azonenberg/dumptruck/dut-breakouts/parallel-nor-csp56/parallel-nor-csp56.kicad_pcb

## KiCad design dut-breakouts/parallel-nor-csp56/parallel-nor-csp56.kicad_pcb (2024-11-30)

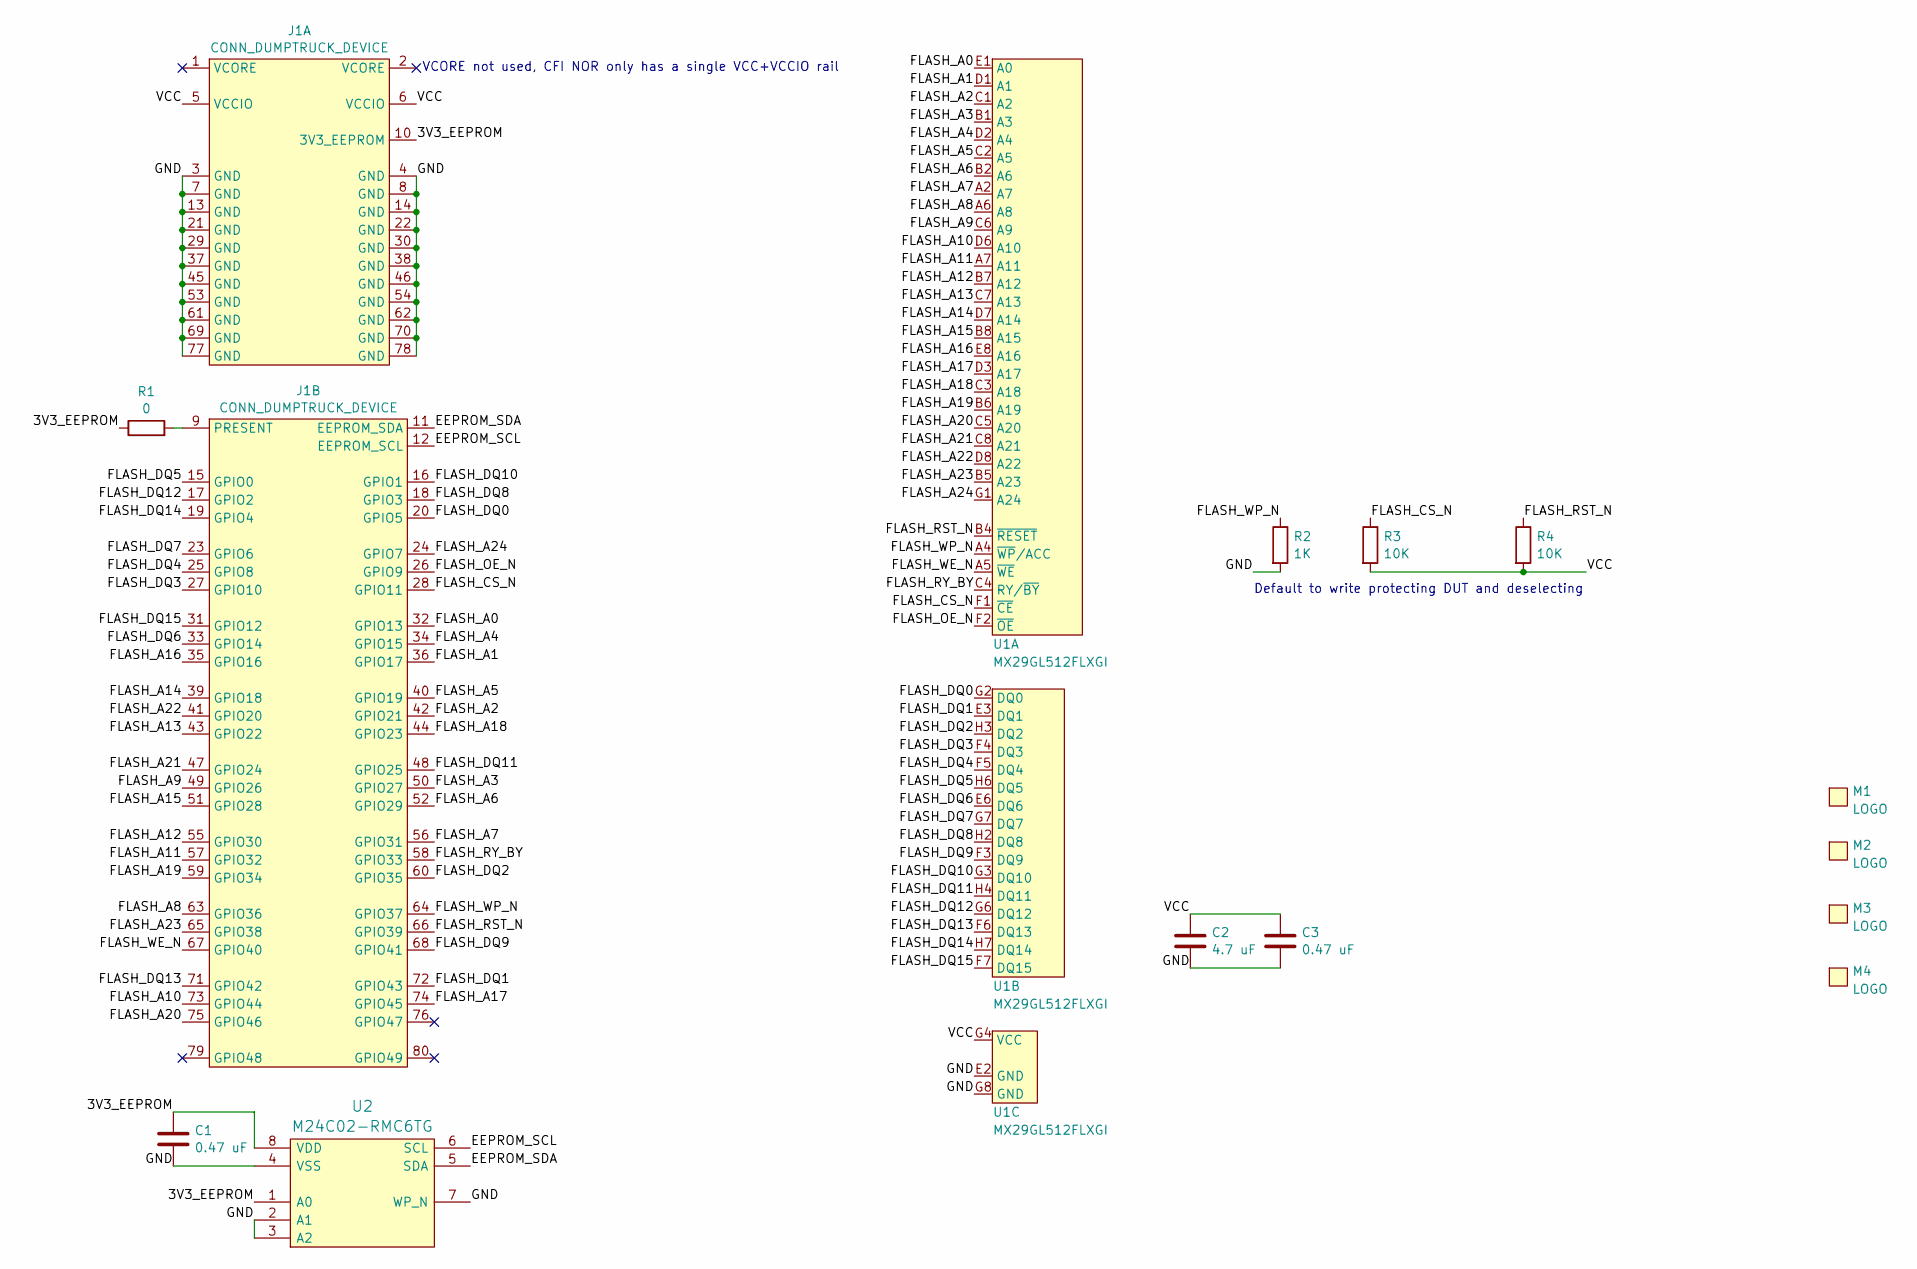
[picture p22: schematic parallel-nor-csp56.kicad_sch]

Parts:
C1, C3: 0.47 uF; EIA_0402_CAP_NOSILK
C2: 4.7 uF; EIA_0603_CAP_NOSILK
J1: CONN_DUMPTRUCK_DEVICE; CONN_SAMTEC_BSE-040-01-L-D-A-TR
M1: LOGO; LONGTHING-1200DPI
M2: LOGO; Logo_silk_ROHS_5x2.8mm
M3: LOGO; Logo_silk_OSHW_6x6mm
M4: LOGO; Logo_silk_WEEE_3.4x5mm
R1: 0; EIA_0402_RES_NOSILK
R2: 1K; EIA_0402_RES_NOSILK
R3, R4: 10K; EIA_0402_RES_NOSILK
U1: MX29GL512FLXGI; BGA_56_6x9_DEPOP_0.8MM_CFI_CSP
U2: M24C02-RMC6TG; DFN_8_0.5MM_2x3MM_TALL

Connections:
/3V3_EEPROM: C1.1, J1.10 (3V3_EEPROM), R1.1, U2.1 (A0), U2.8 (VDD)
/EEPROM_SCL: J1.12 (EEPROM_SCL), U2.6 (SCL)
/EEPROM_SDA: J1.11 (EEPROM_SDA), U2.5 (SDA)
/FLASH_A0: J1.32 (GPIO13), U1.E1 (A0)
/FLASH_A1: J1.36 (GPIO17), U1.D1 (A1)
/FLASH_A2: J1.42 (GPIO21), U1.C1 (A2)
/FLASH_A3: J1.50 (GPIO27), U1.B1 (A3)
/FLASH_A4: J1.34 (GPIO15), U1.D2 (A4)
/FLASH_A5: J1.40 (GPIO19), U1.C2 (A5)
/FLASH_A6: J1.52 (GPIO29), U1.B2 (A6)
/FLASH_A7: J1.56 (GPIO31), U1.A2 (A7)
/FLASH_A8: J1.63 (GPIO36), U1.A6 (A8)
/FLASH_A9: J1.49 (GPIO26), U1.C6 (A9)
/FLASH_A10: J1.73 (GPIO44), U1.D6 (A10)
/FLASH_A11: J1.57 (GPIO32), U1.A7 (A11)
/FLASH_A12: J1.55 (GPIO30), U1.B7 (A12)
/FLASH_A13: J1.43 (GPIO22), U1.C7 (A13)
/FLASH_A14: J1.39 (GPIO18), U1.D7 (A14)
/FLASH_A15: J1.51 (GPIO28), U1.B8 (A15)
/FLASH_A16: J1.35 (GPIO16), U1.E8 (A16)
/FLASH_A17: J1.74 (GPIO45), U1.D3 (A17)
/FLASH_A18: J1.44 (GPIO23), U1.C3 (A18)
/FLASH_A19: J1.59 (GPIO34), U1.B6 (A19)
/FLASH_A20: J1.75 (GPIO46), U1.C5 (A20)
/FLASH_A21: J1.47 (GPIO24), U1.C8 (A21)
/FLASH_A22: J1.41 (GPIO20), U1.D8 (A22)
/FLASH_A23: J1.65 (GPIO38), U1.B5 (A23)
/FLASH_A24: J1.24 (GPIO7), U1.G1 (A24)
/FLASH_CS_N: J1.28 (GPIO11), R3.1, U1.F1 (~CE)
/FLASH_DQ0: J1.20 (GPIO5), U1.G2 (DQ0)
/FLASH_DQ1: J1.72 (GPIO43), U1.E3 (DQ1)
/FLASH_DQ2: J1.60 (GPIO35), U1.H3 (DQ2)
/FLASH_DQ3: J1.27 (GPIO10), U1.F4 (DQ3)
/FLASH_DQ4: J1.25 (GPIO8), U1.F5 (DQ4)
/FLASH_DQ5: J1.15 (GPIO0), U1.H6 (DQ5)
/FLASH_DQ6: J1.33 (GPIO14), U1.E6 (DQ6)
/FLASH_DQ7: J1.23 (GPIO6), U1.G7 (DQ7)
/FLASH_DQ8: J1.18 (GPIO3), U1.H2 (DQ8)
/FLASH_DQ9: J1.68 (GPIO41), U1.F3 (DQ9)
/FLASH_DQ10: J1.16 (GPIO1), U1.G3 (DQ10)
/FLASH_DQ11: J1.48 (GPIO25), U1.H4 (DQ11)
/FLASH_DQ12: J1.17 (GPIO2), U1.G6 (DQ12)
/FLASH_DQ13: J1.71 (GPIO42), U1.F6 (DQ13)
/FLASH_DQ14: J1.19 (GPIO4), U1.H7 (DQ14)
/FLASH_DQ15: J1.31 (GPIO12), U1.F7 (DQ15)
/FLASH_OE_N: J1.26 (GPIO9), U1.F2 (~OE)
/FLASH_RST_N: J1.66 (GPIO39), R4.1, U1.B4 (~RESET)
/FLASH_RY_BY: J1.58 (GPIO33), U1.C4 (RY/~BY)
/FLASH_WE_N: J1.67 (GPIO40), U1.A5 (~WE)
/FLASH_WP_N: J1.64 (GPIO37), R2.1, U1.A4 (~WP/ACC)
/GND: C1.2, C2.2, C3.2, J1.3 (GND), J1.4 (GND), J1.7 (GND), J1.8 (GND), J1.13 (GND), J1.14 (GND), J1.21 (GND), J1.22 (GND), J1.29 (GND), J1.30 (GND), J1.37 (GND), J1.38 (GND), J1.45 (GND), J1.46 (GND), J1.53 (GND), J1.54 (GND), J1.61 (GND), J1.62 (GND), J1.69 (GND), J1.70 (GND), J1.77 (GND), J1.78 (GND), R2.2, U1.E2 (GND), U1.G8 (GND), U2.2 (A1), U2.3 (A2), U2.4 (VSS), U2.7 (WP_N)
/VCC: C2.1, C3.1, J1.5 (VCCIO), J1.6 (VCCIO), R3.2, R4.2, U1.G4 (VCC)
unnamed: J1.9 (PRESENT), R1.2

Notes on the sheet:
VCORE not used, CFI NOR only has a single VCC+VCCIO rail
Default to write protecting DUT and deselecting

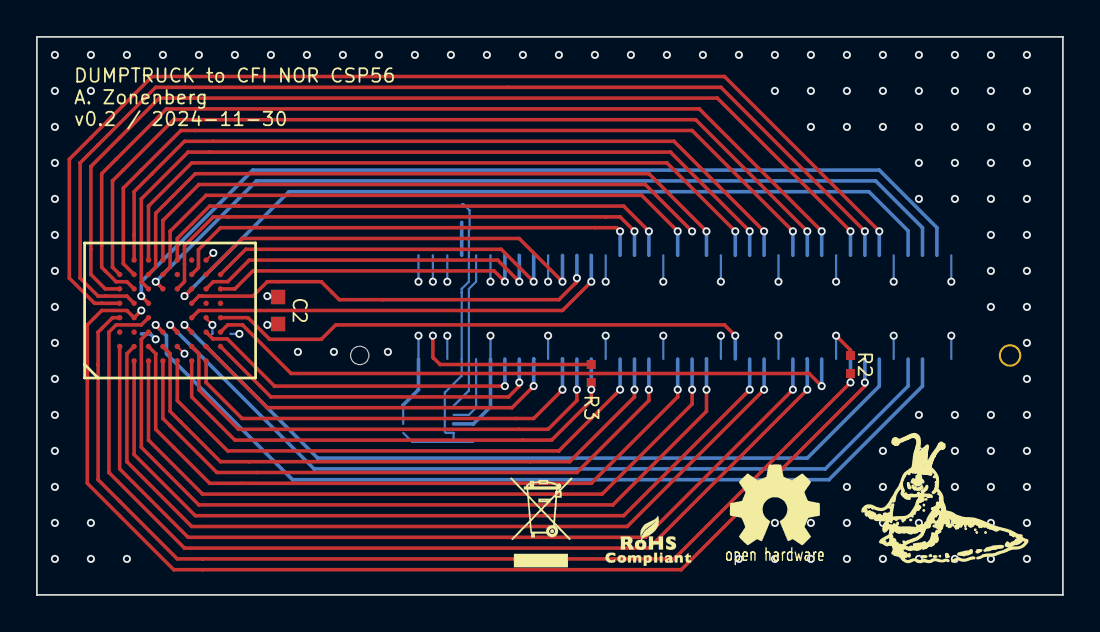
[picture p23: board parallel-nor-csp56.kicad_pcb from above]

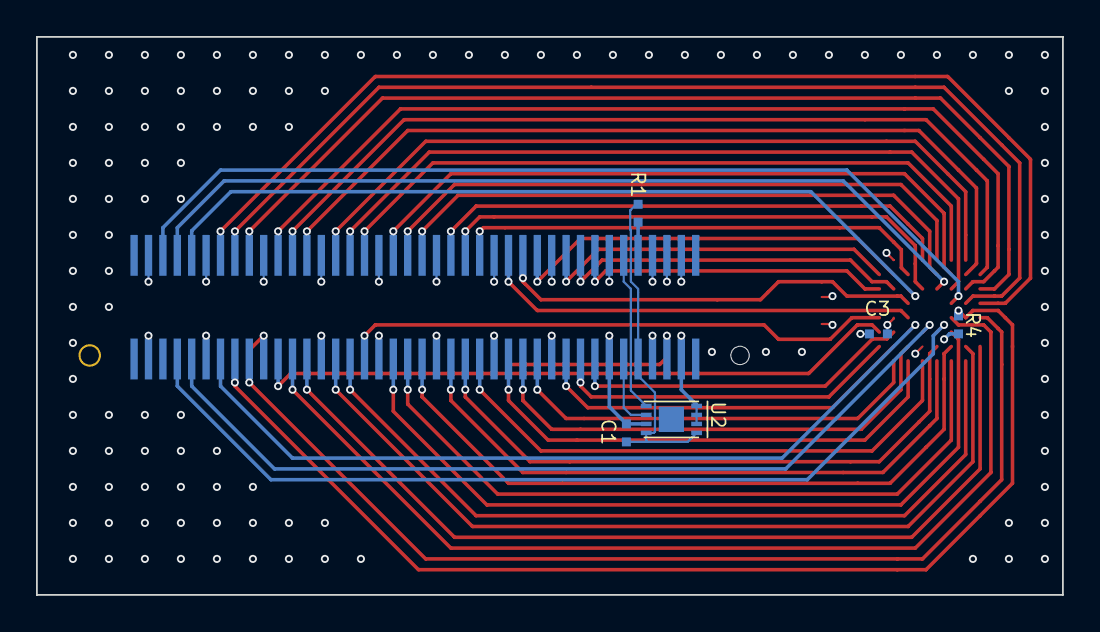
[picture p24: board parallel-nor-csp56.kicad_pcb from below]

Board: 4 copper layers, 57.0 x 31.0 mm, 14 parts (6 on the bottom side), 53 nets.
