azonenberg/dumptruck/jtag-interposer/jtag-interposer.kicad_pcb

## KiCad design jtag-interposer/jtag-interposer.kicad_pcb (2024-11-25)

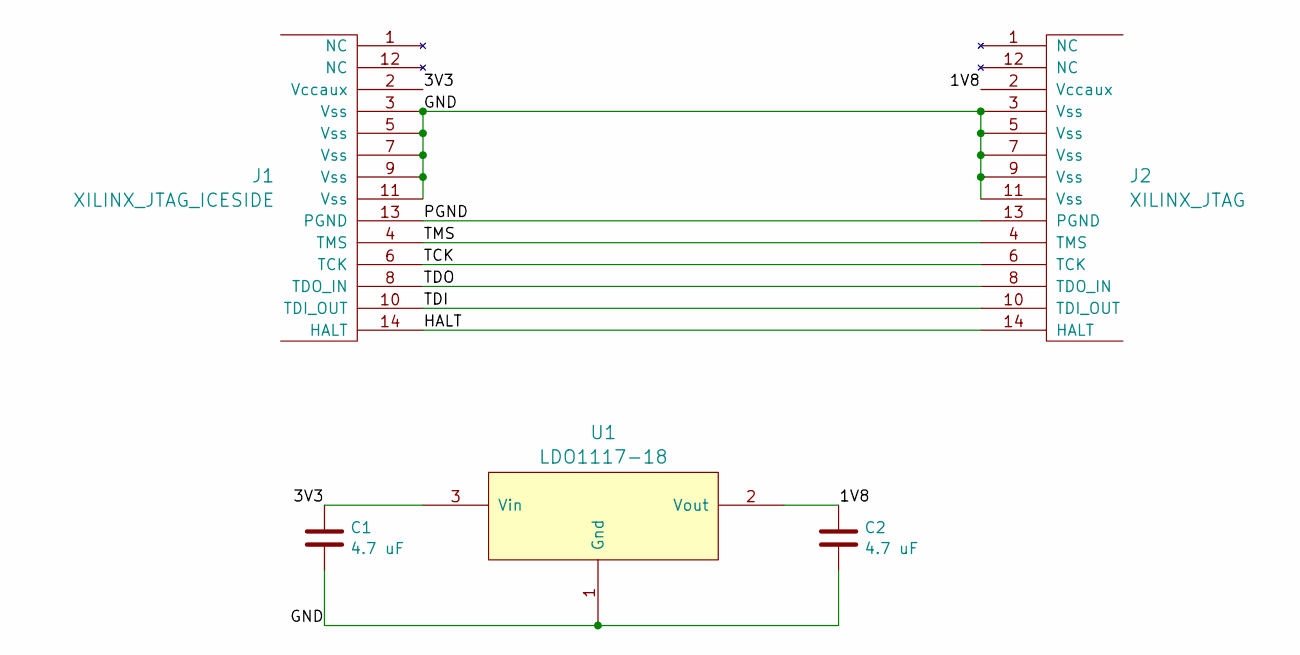
[picture p25: schematic jtag-interposer.kicad_sch]

Parts:
C1, C2: 4.7 uF; EIA_0603_CAP_NOSILK
J1: XILINX_JTAG_ICESIDE; XILINX_JTAG_PTH_MOLEX_0878311420
J2: XILINX_JTAG; XILINX_JTAG_PTH_MOLEX_0878311420
U1: LDO1117-18; SOT223-4

Connections:
/1V8: C2.1, J2.2 (Vccaux), U1.2 (Vout)
/3V3: C1.1, J1.2 (Vccaux), U1.3 (Vin)
/GND: C1.2, C2.2, J1.3 (Vss), J1.5 (Vss), J1.7 (Vss), J1.9 (Vss), J1.11 (Vss), J2.3 (Vss), J2.5 (Vss), J2.7 (Vss), J2.9 (Vss), J2.11 (Vss), U1.1 (Gnd)
/HALT: J1.14 (HALT), J2.14 (HALT)
/PGND: J1.13 (PGND), J2.13 (PGND)
/TCK: J1.6 (TCK), J2.6 (TCK)
/TDI: J1.10 (TDI_OUT), J2.10 (TDI_OUT)
/TDO: J1.8 (TDO_IN), J2.8 (TDO_IN)
/TMS: J1.4 (TMS), J2.4 (TMS)

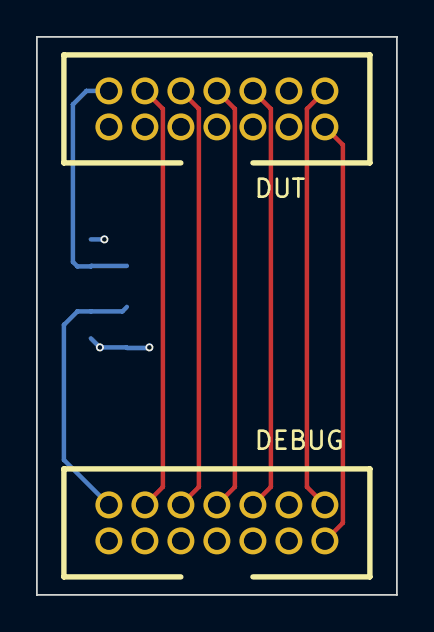
[picture p26: board jtag-interposer.kicad_pcb from above]

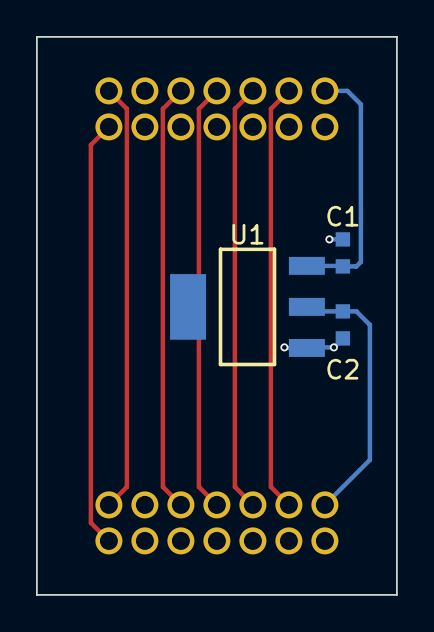
[picture p27: board jtag-interposer.kicad_pcb from below]

Board: 4 copper layers, 20.0 x 31.0 mm, 5 parts (3 on the bottom side), 9 nets.
