azonenberg/dumptruck/main-pcb/main-pcb.kicad_pcb

## KiCad design main-pcb/main-pcb.kicad_pcb (2024-10-24)

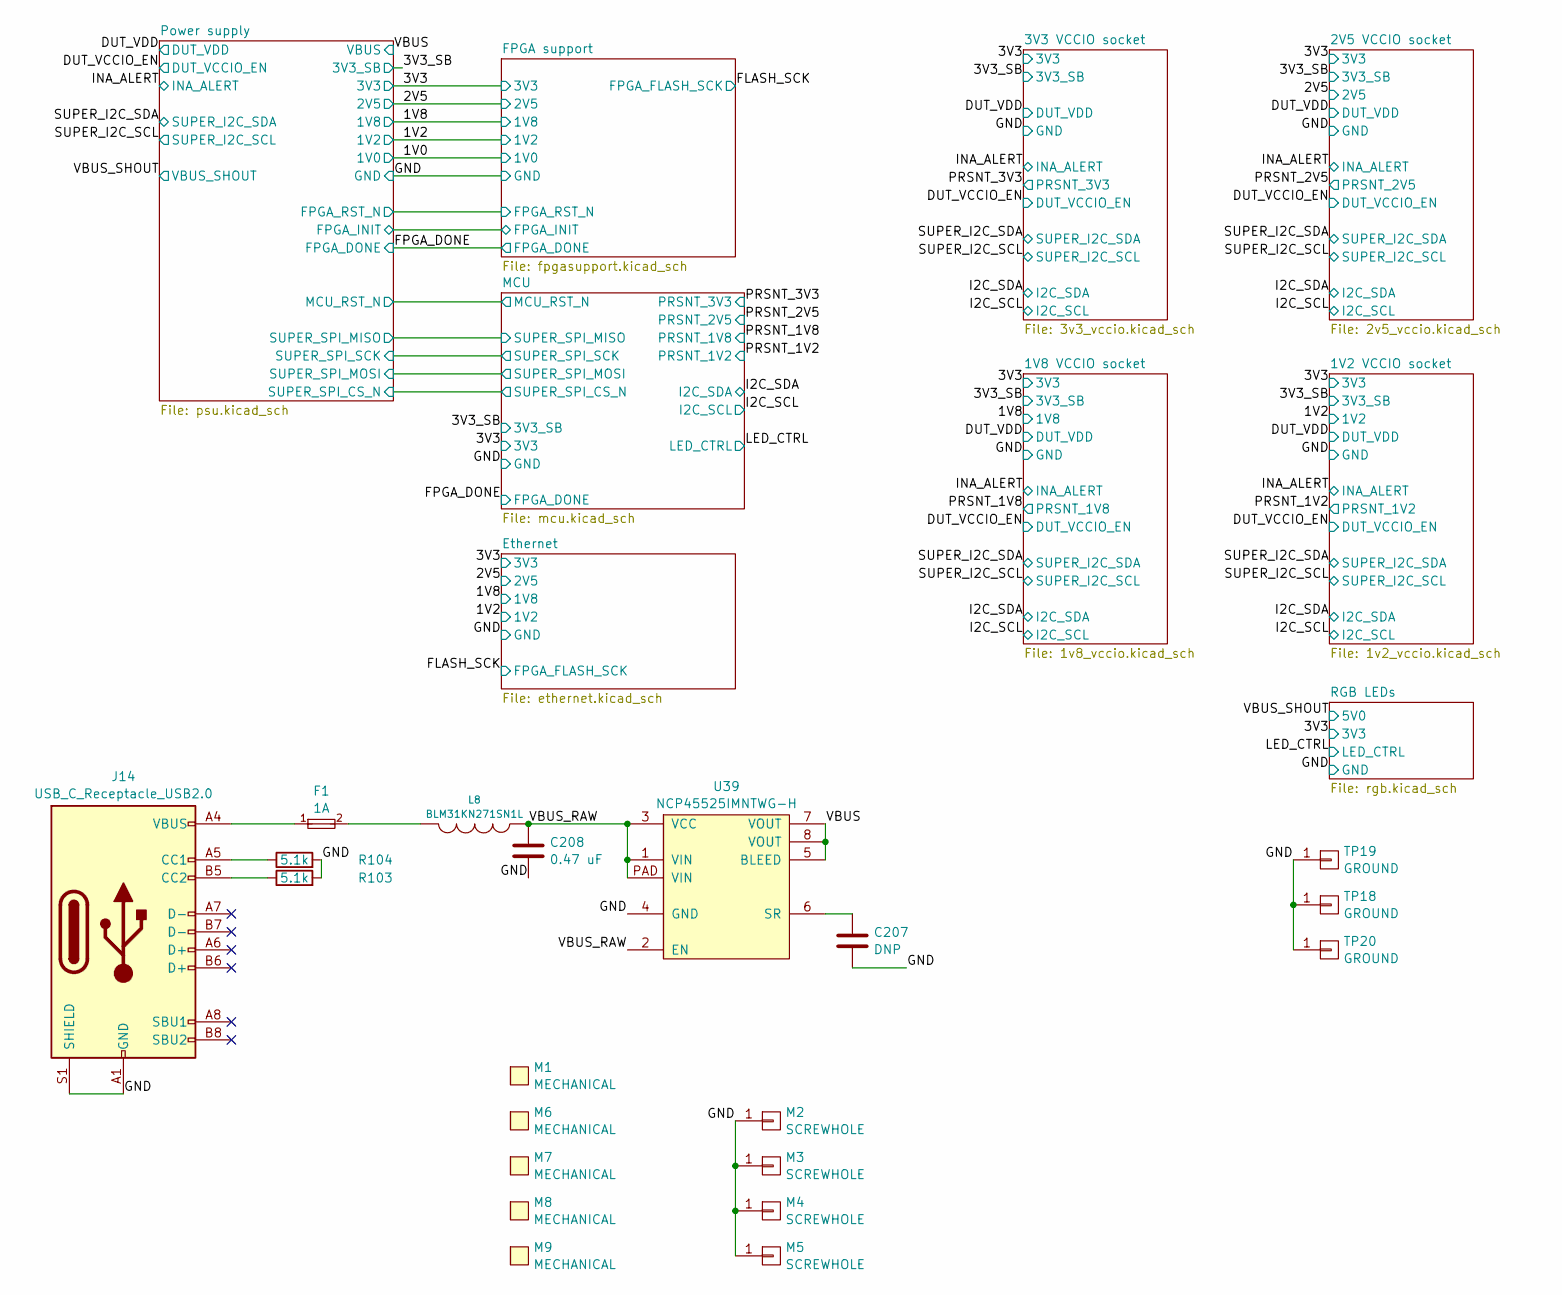
[picture p28: schematic main-pcb.kicad_sch, DUMPTRUCK flash dumper]

Parts:
C207: DNP; EIA_0402_CAP_NOSILK
C208: 0.47 uF; EIA_0402_CAP_NOSILK
F1: 1A; EIA_0402_RES_NOSILK
J14: USB_C_Receptacle_USB2.0; GCT_USB4500-03-0-A
L8: BLM31KN271SN1L; EIA_1206_CAP_NOSILK
M1: MECHANICAL; LONGTHING-1200DPI
M2, M3, M4, M5: SCREWHOLE; MECHANICAL_CLEARANCEHOLE_4_40
M6: MECHANICAL; LOGO_ESD_SENSITIVE_7MM
M7: MECHANICAL; Logo_silk_OSHW_6x6mm
M8: MECHANICAL; Logo_silk_ROHS_5x2.8mm
M9: MECHANICAL; Logo_silk_WEEE_3.4x5mm
R103, R104: 5.1k; EIA_0402_RES_NOSILK
TP18, TP19, TP20: GROUND; TESTPOINT_SMT_KEYSTONE_5016
U39: NCP45525IMNTWG-H; DFN_8_0.5MM_2x2MM

Connections:
/GND: C207.2, C208.2, J14.A1 (GND), J14.A12 (GND), J14.B1 (GND), J14.B12 (GND), J14.S1 (SHIELD), M2.1, M3.1, M4.1, M5.1, R103.2, R104.2, TP18.1, TP19.1, TP20.1, U39.4 (GND); also elsewhere on the board
/VBUS: U39.5 (BLEED), U39.7 (VOUT), U39.8 (VOUT); also elsewhere on the board
/VBUS_RAW: C208.1, L8.1, U39.1 (VIN), U39.2 (EN), U39.3 (VCC), U39.PAD (VIN)
unnamed: F1.1, J14.A4 (VBUS), J14.A9 (VBUS), J14.B4 (VBUS), J14.B9 (VBUS)
unnamed: F1.2, L8.2
unnamed: J14.A5 (CC1), R104.1
unnamed: J14.B5 (CC2), R103.1
unnamed: C207.1, U39.6 (SR)

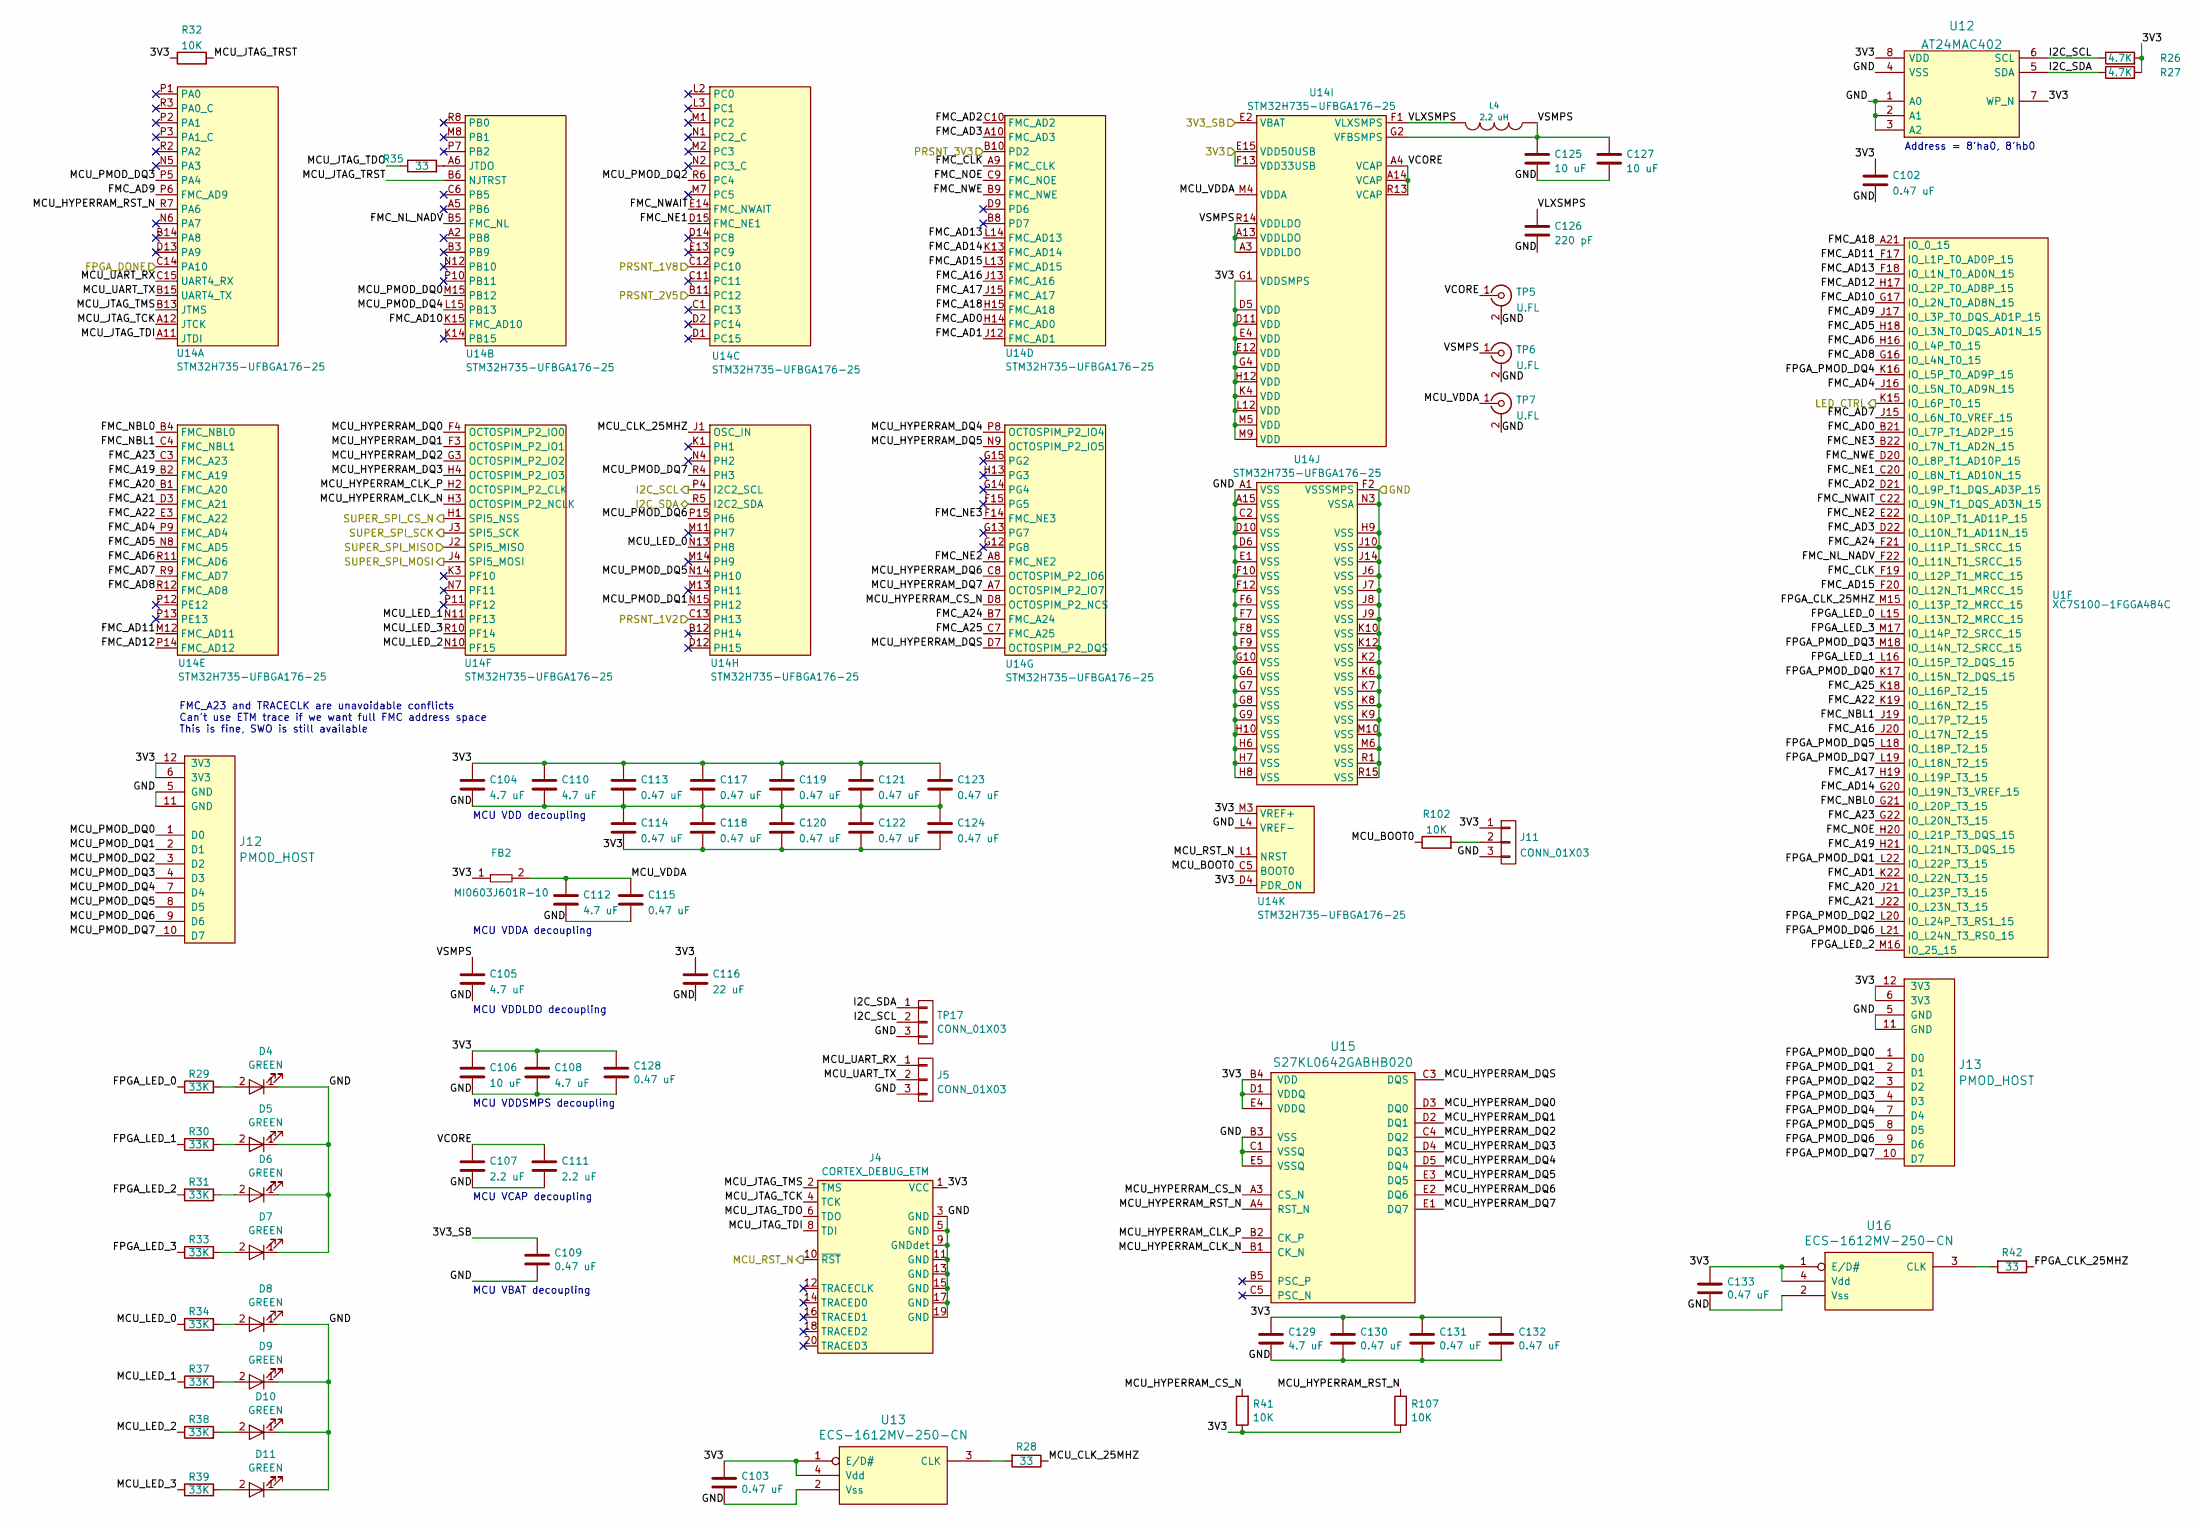
[picture p29: schematic mcu.kicad_sch, DUMPTRUCK flash dumper]

Parts:
C102, C103, C109, C113, C114, C115, C117, C118, C119, C120, C121, C122, C123, C124, C128, C130, C131, C132, C133: 0.47 uF; EIA_0402_CAP_NOSILK
C104, C105, C108, C110, C112, C129: 4.7 uF; EIA_0603_CAP_NOSILK
C106, C125, C127: 10 uF; EIA_0805_CAP_NOSILK
C107, C111: 2.2 uF; EIA_0805_CAP_NOSILK
C116: 22 uF; EIA_0805_CAP_NOSILK
C126: 220 pF; EIA_0402_CAP_NOSILK
D4, D5, D6, D7, D8, D9, D10, D11: GREEN; EIA_0402_LED
FB2: MI0603J601R-10; EIA_0603_INDUCTOR_NOSILK
J4: CORTEX_DEBUG_ETM; CONN_HEADER_1.27MM_2x10_SMT_SAMTEC_FTSH-110-01-L-DV-K
J5, J11: CONN_01X03; CONN_HEADER_2.54MM_1x3
J12, J13: PMOD_HOST; CONN_HEADER_2.54MM_2x6_RA_PMOD_HOST
L4: 2.2 uH; EIA_1210_CAP_NOSILK
R26, R27: 4.7K; EIA_0402_RES_NOSILK
R28, R35, R42: 33; EIA_0402_RES_NOSILK
R29, R30, R31, R33, R34, R37, R38, R39: 33K; EIA_0402_RES_NOSILK
R32, R41, R102, R107: 10K; EIA_0402_RES_NOSILK
TP5, TP6, TP7: U.FL; CONN_U.FL_TE_1909763-1
TP17: CONN_01X03; CONN_HEADER_2.54MM_1x3
U1: XC7S100-1FGGA484C; BGA_484_22x22_FULLARRAY_1MM
U12: AT24MAC402; DFN_8_0.5MM_2x3MM_TALL
U13, U16: ECS-1612MV-250-CN; OSCILLATOR_1.6x1.2
U14: STM32H735-UFBGA176-25; BGA_201_10x10_DEPOP_0.65MM_OSHPARK
U15: S27KL0642GABHB020; BGA_24_6x8_DEPOP1_1MM

Connections:
/3V3: C102.1, C103.1, C104.1, C106.1, C108.1, C110.1, C113.1, C114.2, C116.1, C117.1, C118.2, C119.1, C120.2, C121.1, C122.2, C123.1, C124.2, C128.1, C129.1, C130.1, C131.1, C132.1, C133.1, FB2.1, J4.1 (VCC), J11.1, J12.6 (3V3), J12.12 (3V3), J13.6 (3V3), J13.12 (3V3), R26.2, R27.2, R32.1, R41.1, R107.1, U12.7 (WP_N), U12.8 (VDD), U13.1 (E/D#), U13.4 (Vdd), U14.D4 (PDR_ON), U14.D5 (VDD), U14.D11 (VDD), U14.E4 (VDD), U14.E12 (VDD), U14.E15 (VDD50USB), U14.F13 (VDD33USB), U14.G1 (VDDSMPS), U14.G4 (VDD), U14.H12 (VDD), U14.K4 (VDD), U14.L12 (VDD), U14.M3 (VREF+), U14.M5 (VDD), U14.M9 (VDD), U15.B4 (VDD), U15.D1 (VDDQ), U15.E4 (VDDQ), U16.1 (E/D#), U16.4 (Vdd); also elsewhere on the board
/3V3_SB: C109.1, U14.E2 (VBAT); also elsewhere on the board
/FPGA_DONE: U14.C14 (PA10); also elsewhere on the board
/GND: C102.2, C103.2, C104.2, C105.2, C106.2, C107.2, C108.2, C109.2, C110.2, C111.2, C112.2, C113.2, C114.1, C115.2, C116.2, C117.2, C118.1, C119.2, C120.1, C121.2, C122.1, C123.2, C124.1, C125.2, C126.2, C127.2, C128.2, C129.2, C130.2, C131.2, C132.2, C133.2, D4.1 (K), D5.1 (K), D6.1 (K), D7.1 (K), D8.1 (K), D9.1 (K), D10.1 (K), D11.1 (K), J4.3 (GND), J4.5 (GND), J4.9 (GNDdet), J4.11 (GND), J4.13 (GND), J4.15 (GND), J4.17 (GND), J4.19 (GND), J5.3, J11.3, J12.5 (GND), J12.11 (GND), J13.5 (GND), J13.11 (GND), TP5.2 (Ext), TP6.2 (Ext), TP7.2 (Ext), TP17.3, U12.1 (A0), U12.2 (A1), U12.3 (A2), U12.4 (VSS), U13.2 (Vss), U14.A1 (VSS), U14.A15 (VSS), U14.C2 (VSS), U14.D6 (VSS), U14.D10 (VSS), U14.E1 (VSS), U14.F2 (VSSSMPS), U14.F6 (VSS), U14.F7 (VSS), U14.F8 (VSS), U14.F9 (VSS), U14.F10 (VSS), U14.F12 (VSS), U14.G6 (VSS), U14.G7 (VSS), U14.G8 (VSS), U14.G9 (VSS), U14.G10 (VSS), U14.H6 (VSS), U14.H7 (VSS), U14.H8 (VSS), U14.H9 (VSS), U14.H10 (VSS), U14.J6 (VSS), U14.J7 (VSS), U14.J8 (VSS), U14.J9 (VSS), U14.J10 (VSS), U14.J14 (VSS), U14.K2 (VSS), U14.K6 (VSS), U14.K7 (VSS), U14.K8 (VSS), U14.K9 (VSS), U14.K10 (VSS), U14.K12 (VSS), U14.L4 (VREF-), U14.M6 (VSS), U14.M10 (VSS), U14.N3 (VSSA), U14.R1 (VSS), U14.R15 (VSS), U15.B3 (VSS), U15.C1 (VSSQ), U15.E5 (VSSQ), U16.2 (Vss); also elsewhere on the board
/I2C_SCL: R26.1, TP17.2, U12.6 (SCL), U14.P4 (I2C2_SCL); also elsewhere on the board
/I2C_SDA: R27.1, TP17.1, U12.5 (SDA), U14.R5 (I2C2_SDA); also elsewhere on the board
/LED_CTRL: U1.K15 (IO_L6P_T0_15); also elsewhere on the board
/MCU/FMC_A16: U1.J20 (IO_L17N_T2_15), U14.J13 (FMC_A16)
/MCU/FMC_A17: U1.H19 (IO_L19P_T3_15), U14.J15 (FMC_A17)
/MCU/FMC_A18: U1.A21 (IO_0_15), U14.H15 (FMC_A18)
/MCU/FMC_A19: U1.H21 (IO_L21N_T3_DQS_15), U14.B2 (FMC_A19)
/MCU/FMC_A20: U1.J21 (IO_L23P_T3_15), U14.B1 (FMC_A20)
/MCU/FMC_A21: U1.J22 (IO_L23N_T3_15), U14.D3 (FMC_A21)
/MCU/FMC_A22: U1.K19 (IO_L16N_T2_15), U14.E3 (FMC_A22)
/MCU/FMC_A23: U1.G22 (IO_L20N_T3_15), U14.C3 (FMC_A23)
/MCU/FMC_A24: U1.F21 (IO_L11P_T1_SRCC_15), U14.B7 (FMC_A24)
/MCU/FMC_A25: U1.K18 (IO_L16P_T2_15), U14.C7 (FMC_A25)
/MCU/FMC_AD0: U1.B21 (IO_L7P_T1_AD2P_15), U14.H14 (FMC_AD0)
/MCU/FMC_AD1: U1.K22 (IO_L22N_T3_15), U14.J12 (FMC_AD1)
/MCU/FMC_AD2: U1.D21 (IO_L9P_T1_DQS_AD3P_15), U14.C10 (FMC_AD2)
/MCU/FMC_AD3: U1.D22 (IO_L10N_T1_AD11N_15), U14.A10 (FMC_AD3)
/MCU/FMC_AD4: U1.J16 (IO_L5N_T0_AD9N_15), U14.P9 (FMC_AD4)
/MCU/FMC_AD5: U1.H18 (IO_L3N_T0_DQS_AD1N_15), U14.N8 (FMC_AD5)
/MCU/FMC_AD6: U1.H16 (IO_L4P_T0_15), U14.R11 (FMC_AD6)
/MCU/FMC_AD7: U1.J15 (IO_L6N_T0_VREF_15), U14.R9 (FMC_AD7)
/MCU/FMC_AD8: U1.G16 (IO_L4N_T0_15), U14.R12 (FMC_AD8)
/MCU/FMC_AD9: U1.J17 (IO_L3P_T0_DQS_AD1P_15), U14.P6 (FMC_AD9)
/MCU/FMC_AD10: U1.G17 (IO_L2N_T0_AD8N_15), U14.K15 (FMC_AD10)
/MCU/FMC_AD11: U1.F17 (IO_L1P_T0_AD0P_15), U14.M12 (FMC_AD11)
/MCU/FMC_AD12: U1.H17 (IO_L2P_T0_AD8P_15), U14.P14 (FMC_AD12)
/MCU/FMC_AD13: U1.F18 (IO_L1N_T0_AD0N_15), U14.L14 (FMC_AD13)
/MCU/FMC_AD14: U1.G20 (IO_L19N_T3_VREF_15), U14.K13 (FMC_AD14)
/MCU/FMC_AD15: U1.F20 (IO_L12N_T1_MRCC_15), U14.L13 (FMC_AD15)
/MCU/FMC_CLK: U1.F19 (IO_L12P_T1_MRCC_15), U14.A9 (FMC_CLK)
/MCU/FMC_NBL0: U1.G21 (IO_L20P_T3_15), U14.B4 (FMC_NBL0)
/MCU/FMC_NBL1: U1.J19 (IO_L17P_T2_15), U14.C4 (FMC_NBL1)
/MCU/FMC_NE1: U1.C20 (IO_L8N_T1_AD10N_15), U14.D15 (FMC_NE1)
/MCU/FMC_NE2: U1.E22 (IO_L10P_T1_AD11P_15), U14.A8 (FMC_NE2)
/MCU/FMC_NE3: U1.B22 (IO_L7N_T1_AD2N_15), U14.F14 (FMC_NE3)
/MCU/FMC_NL_NADV: U1.F22 (IO_L11N_T1_SRCC_15), U14.B5 (FMC_NL)
/MCU/FMC_NOE: U1.H20 (IO_L21P_T3_DQS_15), U14.C9 (FMC_NOE)
/MCU/FMC_NWAIT: U1.C22 (IO_L9N_T1_DQS_AD3N_15), U14.E14 (FMC_NWAIT)
/MCU/FMC_NWE: U1.D20 (IO_L8P_T1_AD10P_15), U14.B9 (FMC_NWE)
/MCU/FPGA_CLK_25MHZ: R42.1, U1.M15 (IO_L13P_T2_MRCC_15)
/MCU/FPGA_LED_0: R29.1, U1.L15 (IO_L13N_T2_MRCC_15)
/MCU/FPGA_LED_1: R30.1, U1.L16 (IO_L15P_T2_DQS_15)
/MCU/FPGA_LED_2: R31.1, U1.M16 (IO_25_15)
/MCU/FPGA_LED_3: R33.1, U1.M17 (IO_L14P_T2_SRCC_15)
/MCU/FPGA_PMOD_DQ0: J13.1 (D0), U1.K17 (IO_L15N_T2_DQS_15)
/MCU/FPGA_PMOD_DQ1: J13.2 (D1), U1.L22 (IO_L22P_T3_15)
/MCU/FPGA_PMOD_DQ2: J13.3 (D2), U1.L20 (IO_L24P_T3_RS1_15)
/MCU/FPGA_PMOD_DQ3: J13.4 (D3), U1.M18 (IO_L14N_T2_SRCC_15)
/MCU/FPGA_PMOD_DQ4: J13.7 (D4), U1.K16 (IO_L5P_T0_AD9P_15)
/MCU/FPGA_PMOD_DQ5: J13.8 (D5), U1.L18 (IO_L18P_T2_15)
/MCU/FPGA_PMOD_DQ6: J13.9 (D6), U1.L21 (IO_L24N_T3_RS0_15)
/MCU/FPGA_PMOD_DQ7: J13.10 (D7), U1.L19 (IO_L18N_T2_15)
/MCU/MCU_BOOT0: R102.1, U14.C5 (BOOT0)
/MCU/MCU_CLK_25MHZ: R28.1, U14.J1 (OSC_IN)
/MCU/MCU_HYPERRAM_CLK_N: U14.H3 (OCTOSPIM_P2_NCLK), U15.B1 (CK_N)
/MCU/MCU_HYPERRAM_CLK_P: U14.H2 (OCTOSPIM_P2_CLK), U15.B2 (CK_P)
/MCU/MCU_HYPERRAM_CS_N: R41.2, U14.D8 (OCTOSPIM_P2_NCS), U15.A3 (CS_N)
/MCU/MCU_HYPERRAM_DQ0: U14.F4 (OCTOSPIM_P2_IO0), U15.D3 (DQ0)
/MCU/MCU_HYPERRAM_DQ1: U14.F3 (OCTOSPIM_P2_IO1), U15.D2 (DQ1)
/MCU/MCU_HYPERRAM_DQ2: U14.G3 (OCTOSPIM_P2_IO2), U15.C4 (DQ2)
/MCU/MCU_HYPERRAM_DQ3: U14.H4 (OCTOSPIM_P2_IO3), U15.D4 (DQ3)
/MCU/MCU_HYPERRAM_DQ4: U14.P8 (OCTOSPIM_P2_IO4), U15.D5 (DQ4)
/MCU/MCU_HYPERRAM_DQ5: U14.N9 (OCTOSPIM_P2_IO5), U15.E3 (DQ5)
/MCU/MCU_HYPERRAM_DQ6: U14.C8 (OCTOSPIM_P2_IO6), U15.E2 (DQ6)
/MCU/MCU_HYPERRAM_DQ7: U14.A7 (OCTOSPIM_P2_IO7), U15.E1 (DQ7)
/MCU/MCU_HYPERRAM_DQS: U14.D7 (OCTOSPIM_P2_DQS), U15.C3 (DQS)
/MCU/MCU_HYPERRAM_RST_N: R107.2, U14.R7 (PA6), U15.A4 (RST_N)
/MCU/MCU_JTAG_TCK: J4.4 (TCK), U14.A12 (JTCK)
/MCU/MCU_JTAG_TDI: J4.8 (TDI), U14.A11 (JTDI)
/MCU/MCU_JTAG_TDO: J4.6 (TDO), R35.1
/MCU/MCU_JTAG_TMS: J4.2 (TMS), U14.B13 (JTMS)
/MCU/MCU_JTAG_TRST: R32.2, U14.B6 (NJTRST)
/MCU/MCU_LED_0: R34.1, U14.N13 (PH8)
/MCU/MCU_LED_1: R37.1, U14.N11 (PF13)
/MCU/MCU_LED_2: R38.1, U14.N10 (PF15)
/MCU/MCU_LED_3: R39.1, U14.R10 (PF14)
/MCU/MCU_PMOD_DQ0: J12.1 (D0), U14.M15 (PB12)
/MCU/MCU_PMOD_DQ1: J12.2 (D1), U14.N15 (PH12)
/MCU/MCU_PMOD_DQ2: J12.3 (D2), U14.R6 (PC4)
/MCU/MCU_PMOD_DQ3: J12.4 (D3), U14.P5 (PA4)
/MCU/MCU_PMOD_DQ4: J12.7 (D4), U14.L15 (PB13)
/MCU/MCU_PMOD_DQ5: J12.8 (D5), U14.N14 (PH10)
/MCU/MCU_PMOD_DQ6: J12.9 (D6), U14.P15 (PH6)
/MCU/MCU_PMOD_DQ7: J12.10 (D7), U14.R4 (PH3)
/MCU/MCU_RST_N: J4.10 (~RST), U14.L1 (NRST); also elsewhere on the board
/MCU/MCU_UART_RX: J5.1, U14.C15 (UART4_RX)
/MCU/MCU_UART_TX: J5.2, U14.B15 (UART4_TX)
/MCU/MCU_VDDA: C112.1, C115.1, FB2.2, TP7.1 (In), U14.M4 (VDDA)
/MCU/SUPER_SPI_CS_N: U14.H1 (SPI5_NSS); also elsewhere on the board
/MCU/SUPER_SPI_MISO: U14.J2 (SPI5_MISO); also elsewhere on the board
/MCU/SUPER_SPI_MOSI: U14.J4 (SPI5_MOSI); also elsewhere on the board
/MCU/SUPER_SPI_SCK: U14.J3 (SPI5_SCK); also elsewhere on the board
/MCU/VCORE: C107.1, C111.1, TP5.1 (In), U14.A4 (VCAP), U14.A14 (VCAP), U14.R13 (VCAP)
/MCU/VLXSMPS: C126.1, L4.2, U14.F1 (VLXSMPS)
/MCU/VSMPS: C105.1, C125.1, C127.1, L4.1, TP6.1 (In), U14.A3 (VDDLDO), U14.A13 (VDDLDO), U14.G2 (VFBSMPS), U14.R14 (VDDLDO)
/PRSNT_1V2: U14.C13 (PH13); also elsewhere on the board
/PRSNT_1V8: U14.C12 (PC10); also elsewhere on the board
/PRSNT_2V5: U14.B11 (PC12); also elsewhere on the board
/PRSNT_3V3: U14.B10 (PD2); also elsewhere on the board
unnamed: D4.2 (A), R29.2
unnamed: D5.2 (A), R30.2
unnamed: D6.2 (A), R31.2
unnamed: D7.2 (A), R33.2
unnamed: D8.2 (A), R34.2
unnamed: D9.2 (A), R37.2
unnamed: D10.2 (A), R38.2
unnamed: D11.2 (A), R39.2
unnamed: J11.2, R102.2
unnamed: R28.2, U13.3 (CLK)
unnamed: R35.2, U14.A6 (JTDO)
unnamed: R42.2, U16.3 (CLK)

Notes on the sheet:
MCU VDDLDO decoupling
MCU VDD decoupling
MCU VDDSMPS decoupling
MCU VDDA decoupling
MCU VCAP decoupling
Address = 8'ha0, 8'hb0
MCU VBAT decoupling
FMC_A23 and TRACECLK are unavoidable conflicts Can't use ETM trace if we want full FMC address space This is fine, SWO is still available
