azonenberg/dumptruck/main-pcb/main-pcb.kicad_pcb

## KiCad design main-pcb/main-pcb.kicad_pcb (continued)

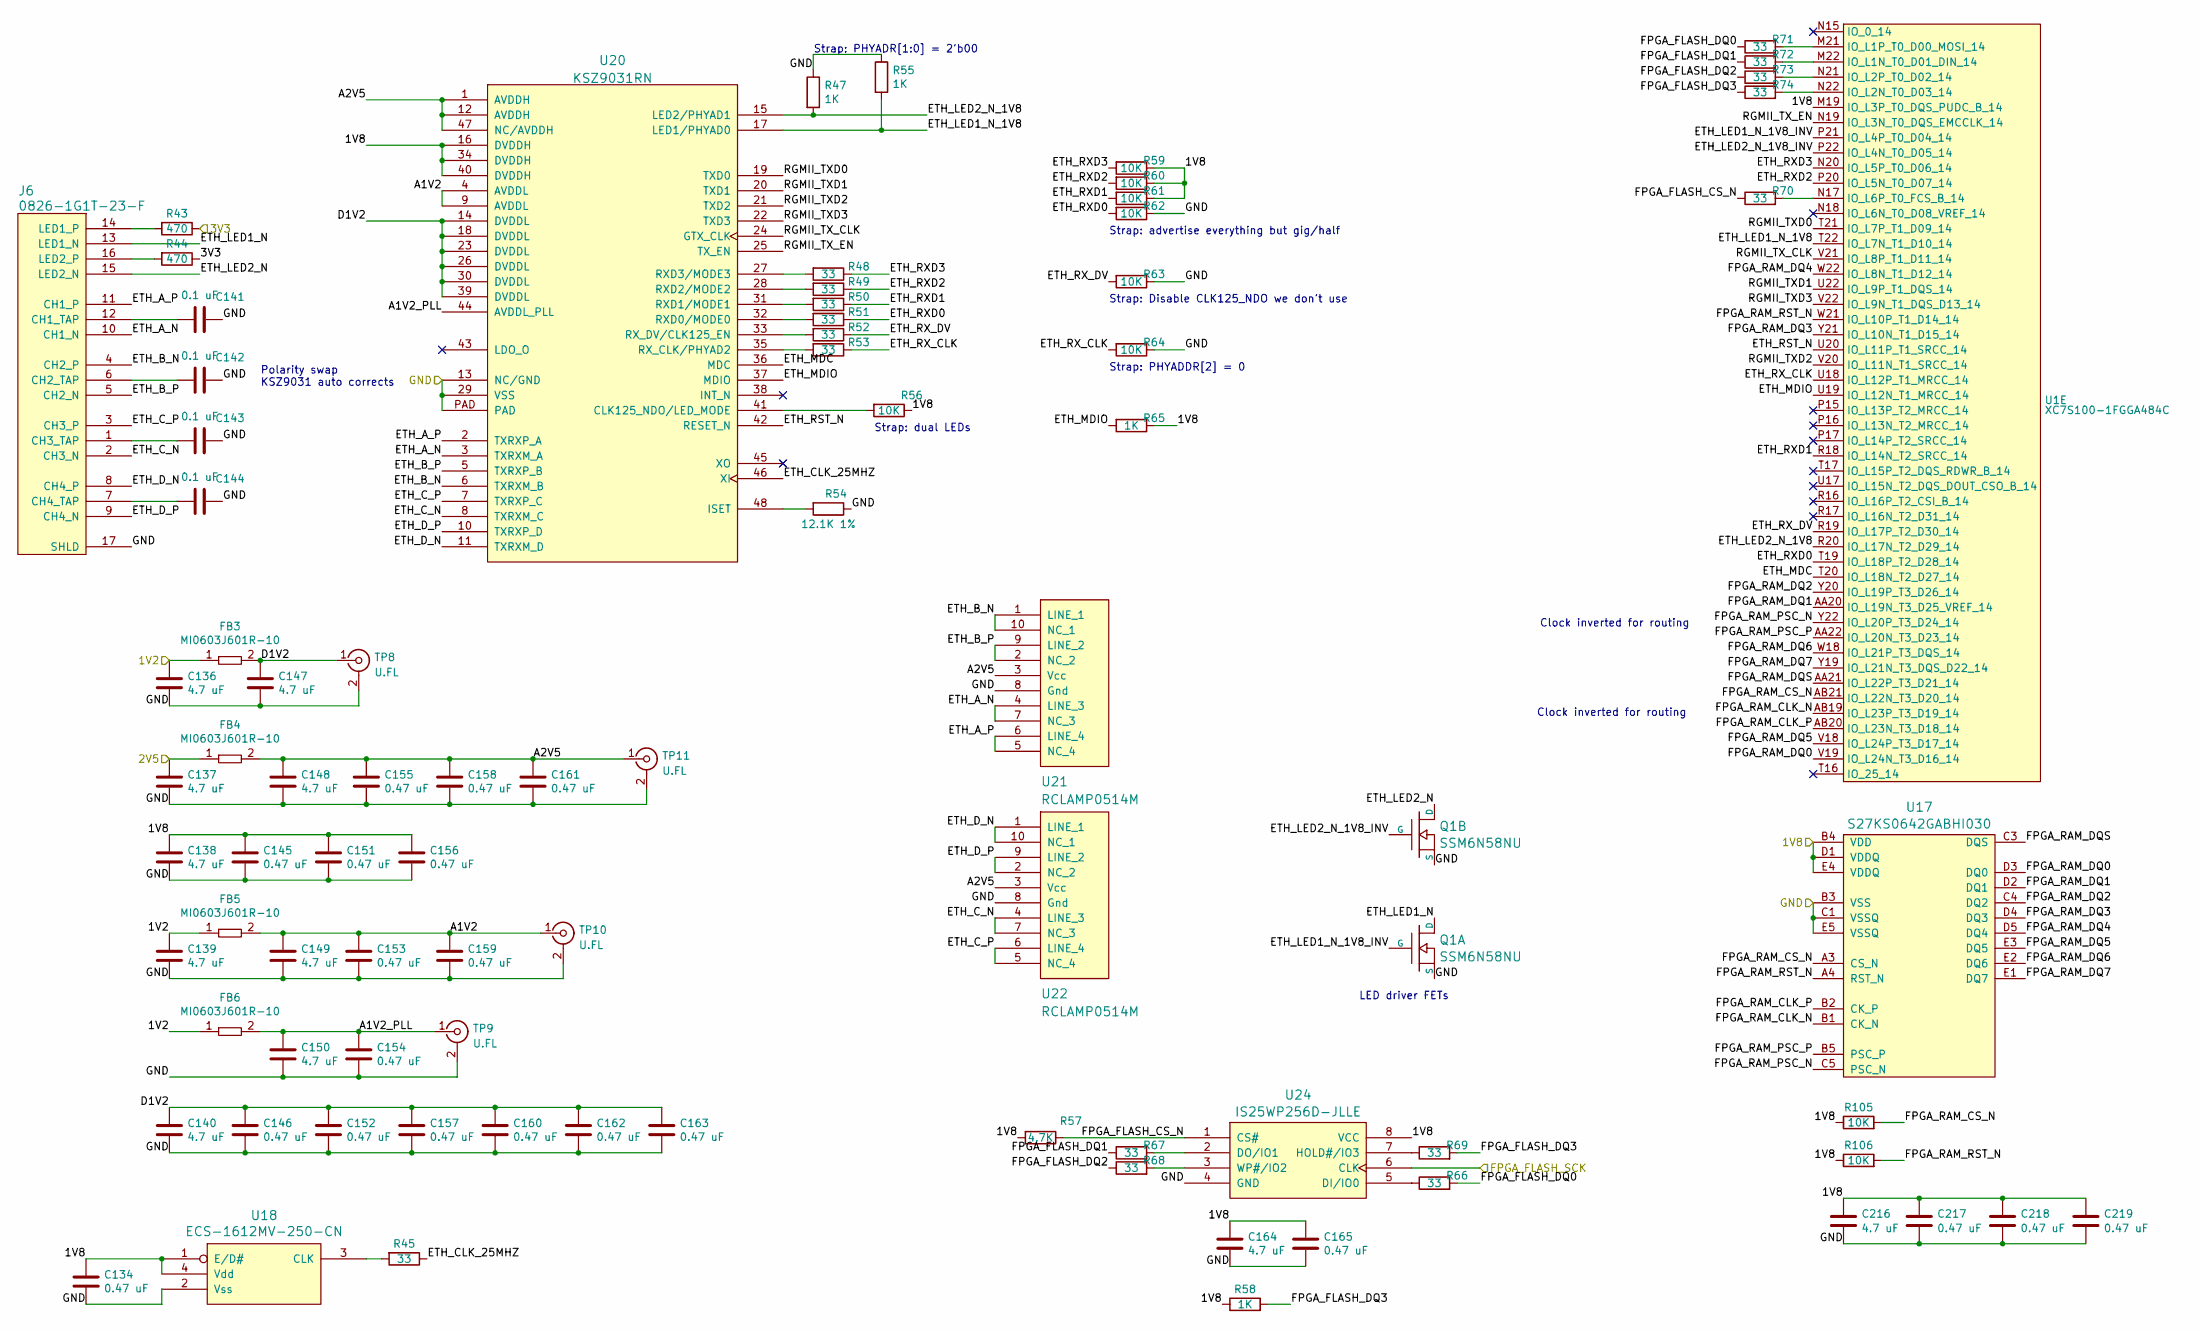
[picture p30: schematic ethernet.kicad_sch, DUMPTRUCK flash dumper]

Parts:
C134, C145, C146, C151, C152, C153, C154, C155, C156, C157, C158, C159, C160, C161, C162, C163, C165, C217, C218, C219: 0.47 uF; EIA_0402_CAP_NOSILK
C136, C137, C138, C139, C140, C147, C148, C149, C150, C164, C216: 4.7 uF; EIA_0603_CAP_NOSILK
C141, C142, C143, C144: 0.1 uF; EIA_0402_CAP_NOSILK
FB3, FB4, FB5, FB6: MI0603J601R-10; EIA_0603_INDUCTOR_NOSILK
J6: 0826-1G1T-23-F; CONN_BELFUSE_0826_1G1T_23_F
Q1: SSM6N58NU; DFN_6_0.65MM_2x2MM_GDS
R43, R44: 470; EIA_0402_RES_NOSILK
R45, R48, R49, R50, R51, R52, R53, R66, R67, R68, R69, R70, R71, R72, R73, R74: 33; EIA_0402_RES_NOSILK
R47, R55, R58, R65: 1K; EIA_0402_RES_NOSILK
R54: 12.1K 1%; EIA_0402_RES_NOSILK
R56, R59, R60, R61, R62, R63, R64, R105, R106: 10K; EIA_0402_RES_NOSILK
R57: 4.7K; EIA_0402_RES_NOSILK
TP8, TP9, TP10, TP11: U.FL; CONN_U.FL_TE_1909763-1
U1: XC7S100-1FGGA484C; BGA_484_22x22_FULLARRAY_1MM
U17: S27KS0642GABHI030; BGA_24_6x8_DEPOP1_1MM
U18: ECS-1612MV-250-CN; OSCILLATOR_1.6x1.2
U20: KSZ9031RN; QFN_48_0.5MM_7x7MM
U21, U22: RCLAMP0514M; SOP_10_0.5MM_3MM
U24: IS25WP256D-JLLE; DFN_8_1.27MM_8x6MM

Connections:
/1V2: C136.1, C139.1, FB3.1, FB5.1, FB6.1; also elsewhere on the board
/1V8: C134.1, C138.1, C145.1, C151.1, C156.1, C164.1, C165.1, C216.1, C217.1, C218.1, C219.1, R56.1, R57.2, R58.1, R59.1, R60.1, R61.1, R65.1, R105.1, R106.1, U1.M19 (IO_L3P_T0_DQS_PUDC_B_14), U17.B4 (VDD), U17.D1 (VDDQ), U17.E4 (VDDQ), U18.1 (E/D#), U18.4 (Vdd), U20.16 (DVDDH), U20.34 (DVDDH), U20.40 (DVDDH), U24.8 (VCC); also elsewhere on the board
/2V5: C137.1, FB4.1; also elsewhere on the board
/3V3: R43.1, R44.1; also elsewhere on the board
/Ethernet/A1V2: C149.1, C153.1, C159.1, FB5.2, TP10.1 (In), U20.4 (AVDDL), U20.9 (AVDDL)
/Ethernet/A1V2_PLL: C150.1, C154.1, FB6.2, TP9.1 (In), U20.44 (AVDDL_PLL)
/Ethernet/A2V5: C148.1, C155.1, C158.1, C161.1, FB4.2, TP11.1 (In), U20.1 (AVDDH), U20.12 (AVDDH), U20.47 (NC/AVDDH), U21.3 (Vcc), U22.3 (Vcc)
/Ethernet/D1V2: C140.1, C146.1, C147.1, C152.1, C157.1, C160.1, C162.1, C163.1, FB3.2, TP8.1 (In), U20.14 (DVDDL), U20.18 (DVDDL), U20.23 (DVDDL), U20.26 (DVDDL), U20.30 (DVDDL), U20.39 (DVDDL)
/Ethernet/ETH_A_N: J6.10 (CH1_N), U20.3 (TXRXM_A), U21.4 (LINE_3), U21.7 (NC_3)
/Ethernet/ETH_A_P: J6.11 (CH1_P), U20.2 (TXRXP_A), U21.5 (NC_4), U21.6 (LINE_4)
/Ethernet/ETH_B_N: J6.4 (CH2_P), U20.6 (TXRXM_B), U21.1 (LINE_1), U21.10 (NC_1)
/Ethernet/ETH_B_P: J6.5 (CH2_N), U20.5 (TXRXP_B), U21.2 (NC_2), U21.9 (LINE_2)
/Ethernet/ETH_CLK_25MHZ: R45.1, U20.46 (XI)
/Ethernet/ETH_C_N: J6.2 (CH3_N), U20.8 (TXRXM_C), U22.4 (LINE_3), U22.7 (NC_3)
/Ethernet/ETH_C_P: J6.3 (CH3_P), U20.7 (TXRXP_C), U22.5 (NC_4), U22.6 (LINE_4)
/Ethernet/ETH_D_N: J6.8 (CH4_P), U20.11 (TXRXM_D), U22.1 (LINE_1), U22.10 (NC_1)
/Ethernet/ETH_D_P: J6.9 (CH4_N), U20.10 (TXRXP_D), U22.2 (NC_2), U22.9 (LINE_2)
/Ethernet/ETH_LED1_N: J6.13 (LED1_N), Q1.D1 (D)
/Ethernet/ETH_LED1_N_1V8: R55.2, U1.T22 (IO_L7N_T1_D10_14), U20.17 (LED1/PHYAD0)
/Ethernet/ETH_LED1_N_1V8_INV: Q1.G1 (G), U1.P21 (IO_L4P_T0_D04_14)
/Ethernet/ETH_LED2_N: J6.15 (LED2_N), Q1.D2 (D)
/Ethernet/ETH_LED2_N_1V8: R47.2, U1.R20 (IO_L17N_T2_D29_14), U20.15 (LED2/PHYAD1)
/Ethernet/ETH_LED2_N_1V8_INV: Q1.G2 (G), U1.P22 (IO_L4N_T0_D05_14)
/Ethernet/ETH_MDC: U1.T20 (IO_L18N_T2_D27_14), U20.36 (MDC)
/Ethernet/ETH_MDIO: R65.2, U1.U19 (IO_L12N_T1_MRCC_14), U20.37 (MDIO)
/Ethernet/ETH_RST_N: U1.U20 (IO_L11P_T1_SRCC_14), U20.42 (RESET_N)
/Ethernet/ETH_RXD0: R51.1, R62.2, U1.T19 (IO_L18P_T2_D28_14)
/Ethernet/ETH_RXD1: R50.1, R61.2, U1.R18 (IO_L14N_T2_SRCC_14)
/Ethernet/ETH_RXD2: R49.1, R60.2, U1.P20 (IO_L5N_T0_D07_14)
/Ethernet/ETH_RXD3: R48.1, R59.2, U1.N20 (IO_L5P_T0_D06_14)
/Ethernet/ETH_RX_CLK: R53.1, R64.2, U1.U18 (IO_L12P_T1_MRCC_14)
/Ethernet/ETH_RX_DV: R52.1, R63.2, U1.R19 (IO_L17P_T2_D30_14)
/Ethernet/FPGA_FLASH_CS_N: R57.1, R70.1, U24.1 (CS#)
/Ethernet/FPGA_FLASH_DQ0: R66.2, R71.1
/Ethernet/FPGA_FLASH_DQ1: R67.1, R72.1
/Ethernet/FPGA_FLASH_DQ2: R68.1, R73.1
/Ethernet/FPGA_FLASH_DQ3: R58.2, R69.2, R74.1
/Ethernet/FPGA_RAM_CLK_N: U1.AB19 (IO_L23P_T3_D19_14), U17.B1 (CK_N)
/Ethernet/FPGA_RAM_CLK_P: U1.AB20 (IO_L23N_T3_D18_14), U17.B2 (CK_P)
/Ethernet/FPGA_RAM_CS_N: R105.2, U1.AB21 (IO_L22N_T3_D20_14), U17.A3 (CS_N)
/Ethernet/FPGA_RAM_DQ0: U1.V19 (IO_L24N_T3_D16_14), U17.D3 (DQ0)
/Ethernet/FPGA_RAM_DQ1: U1.AA20 (IO_L19N_T3_D25_VREF_14), U17.D2 (DQ1)
/Ethernet/FPGA_RAM_DQ2: U1.Y20 (IO_L19P_T3_D26_14), U17.C4 (DQ2)
/Ethernet/FPGA_RAM_DQ3: U1.Y21 (IO_L10N_T1_D15_14), U17.D4 (DQ3)
/Ethernet/FPGA_RAM_DQ4: U1.W22 (IO_L8N_T1_D12_14), U17.D5 (DQ4)
/Ethernet/FPGA_RAM_DQ5: U1.V18 (IO_L24P_T3_D17_14), U17.E3 (DQ5)
/Ethernet/FPGA_RAM_DQ6: U1.W18 (IO_L21P_T3_DQS_14), U17.E2 (DQ6)
/Ethernet/FPGA_RAM_DQ7: U1.Y19 (IO_L21N_T3_DQS_D22_14), U17.E1 (DQ7)
/Ethernet/FPGA_RAM_DQS: U1.AA21 (IO_L22P_T3_D21_14), U17.C3 (DQS)
/Ethernet/FPGA_RAM_PSC_N: U1.Y22 (IO_L20P_T3_D24_14), U17.C5 (PSC_N)
/Ethernet/FPGA_RAM_PSC_P: U1.AA22 (IO_L20N_T3_D23_14), U17.B5 (PSC_P)
/Ethernet/FPGA_RAM_RST_N: R106.2, U1.W21 (IO_L10P_T1_D14_14), U17.A4 (RST_N)
/Ethernet/RGMII_TXD0: U1.T21 (IO_L7P_T1_D09_14), U20.19 (TXD0)
/Ethernet/RGMII_TXD1: U1.U22 (IO_L9P_T1_DQS_14), U20.20 (TXD1)
/Ethernet/RGMII_TXD2: U1.V20 (IO_L11N_T1_SRCC_14), U20.21 (TXD2)
/Ethernet/RGMII_TXD3: U1.V22 (IO_L9N_T1_DQS_D13_14), U20.22 (TXD3)
/Ethernet/RGMII_TX_CLK: U1.V21 (IO_L8P_T1_D11_14), U20.24 (GTX_CLK)
/Ethernet/RGMII_TX_EN: U1.N19 (IO_L3N_T0_DQS_EMCCLK_14), U20.25 (TX_EN)
/FLASH_SCK: U24.6 (CLK); also elsewhere on the board
/GND: C134.2, C136.2, C137.2, C138.2, C139.2, C140.2, C141.1, C142.1, C143.1, C144.1, C145.2, C146.2, C147.2, C148.2, C149.2, C150.2, C151.2, C152.2, C153.2, C154.2, C155.2, C156.2, C157.2, C158.2, C159.2, C160.2, C161.2, C162.2, C163.2, C164.2, C165.2, C216.2, C217.2, C218.2, C219.2, J6.17 (SHLD), Q1.S1 (S), Q1.S2 (S), R47.1, R54.1, R55.1, R62.1, R63.1, R64.1, TP8.2 (Ext), TP9.2 (Ext), TP10.2 (Ext), TP11.2 (Ext), U17.B3 (VSS), U17.C1 (VSSQ), U17.E5 (VSSQ), U18.2 (Vss), U20.13 (NC/GND), U20.29 (VSS), U20.PAD, U21.8 (Gnd), U22.8 (Gnd), U24.4 (GND); also elsewhere on the board
unnamed: C141.2, J6.12 (CH1_TAP)
unnamed: C142.2, J6.6 (CH2_TAP)
unnamed: C143.2, J6.1 (CH3_TAP)
unnamed: C144.2, J6.7 (CH4_TAP)
unnamed: J6.14 (LED1_P), R43.2
unnamed: J6.16 (LED2_P), R44.2
unnamed: R72.2, U1.M22 (IO_L1N_T0_D01_DIN_14)
unnamed: R71.2, U1.M21 (IO_L1P_T0_D00_MOSI_14)
unnamed: R74.2, U1.N22 (IO_L2N_T0_D03_14)
unnamed: R73.2, U1.N21 (IO_L2P_T0_D02_14)
unnamed: R70.2, U1.N17 (IO_L6P_T0_FCS_B_14)
unnamed: R45.2, U18.3 (CLK)
unnamed: R56.2, U20.41 (CLK125_NDO/LED_MODE)
unnamed: R54.2, U20.48 (ISET)
unnamed: R51.2, U20.32 (RXD0/MODE0)
unnamed: R50.2, U20.31 (RXD1/MODE1)
unnamed: R49.2, U20.28 (RXD2/MODE2)
unnamed: R48.2, U20.27 (RXD3/MODE3)
unnamed: R53.2, U20.35 (RX_CLK/PHYAD2)
unnamed: R52.2, U20.33 (RX_DV/CLK125_EN)
unnamed: R66.1, U24.5 (DI/IO0)
unnamed: R67.2, U24.2 (DO/IO1)
unnamed: R69.1, U24.7 (HOLD#/IO3)
unnamed: R68.2, U24.3 (WP#/IO2)

Notes on the sheet:
Strap: Disable CLK125_NDO we don't use
Strap: dual LEDs
Strap: PHYADDR[2] = 0
LED driver FETs
Polarity swap KSZ9031 auto corrects
Strap: advertise everything but gig/half
Clock inverted for routing
Strap: PHYADR[1:0] = 2'b00

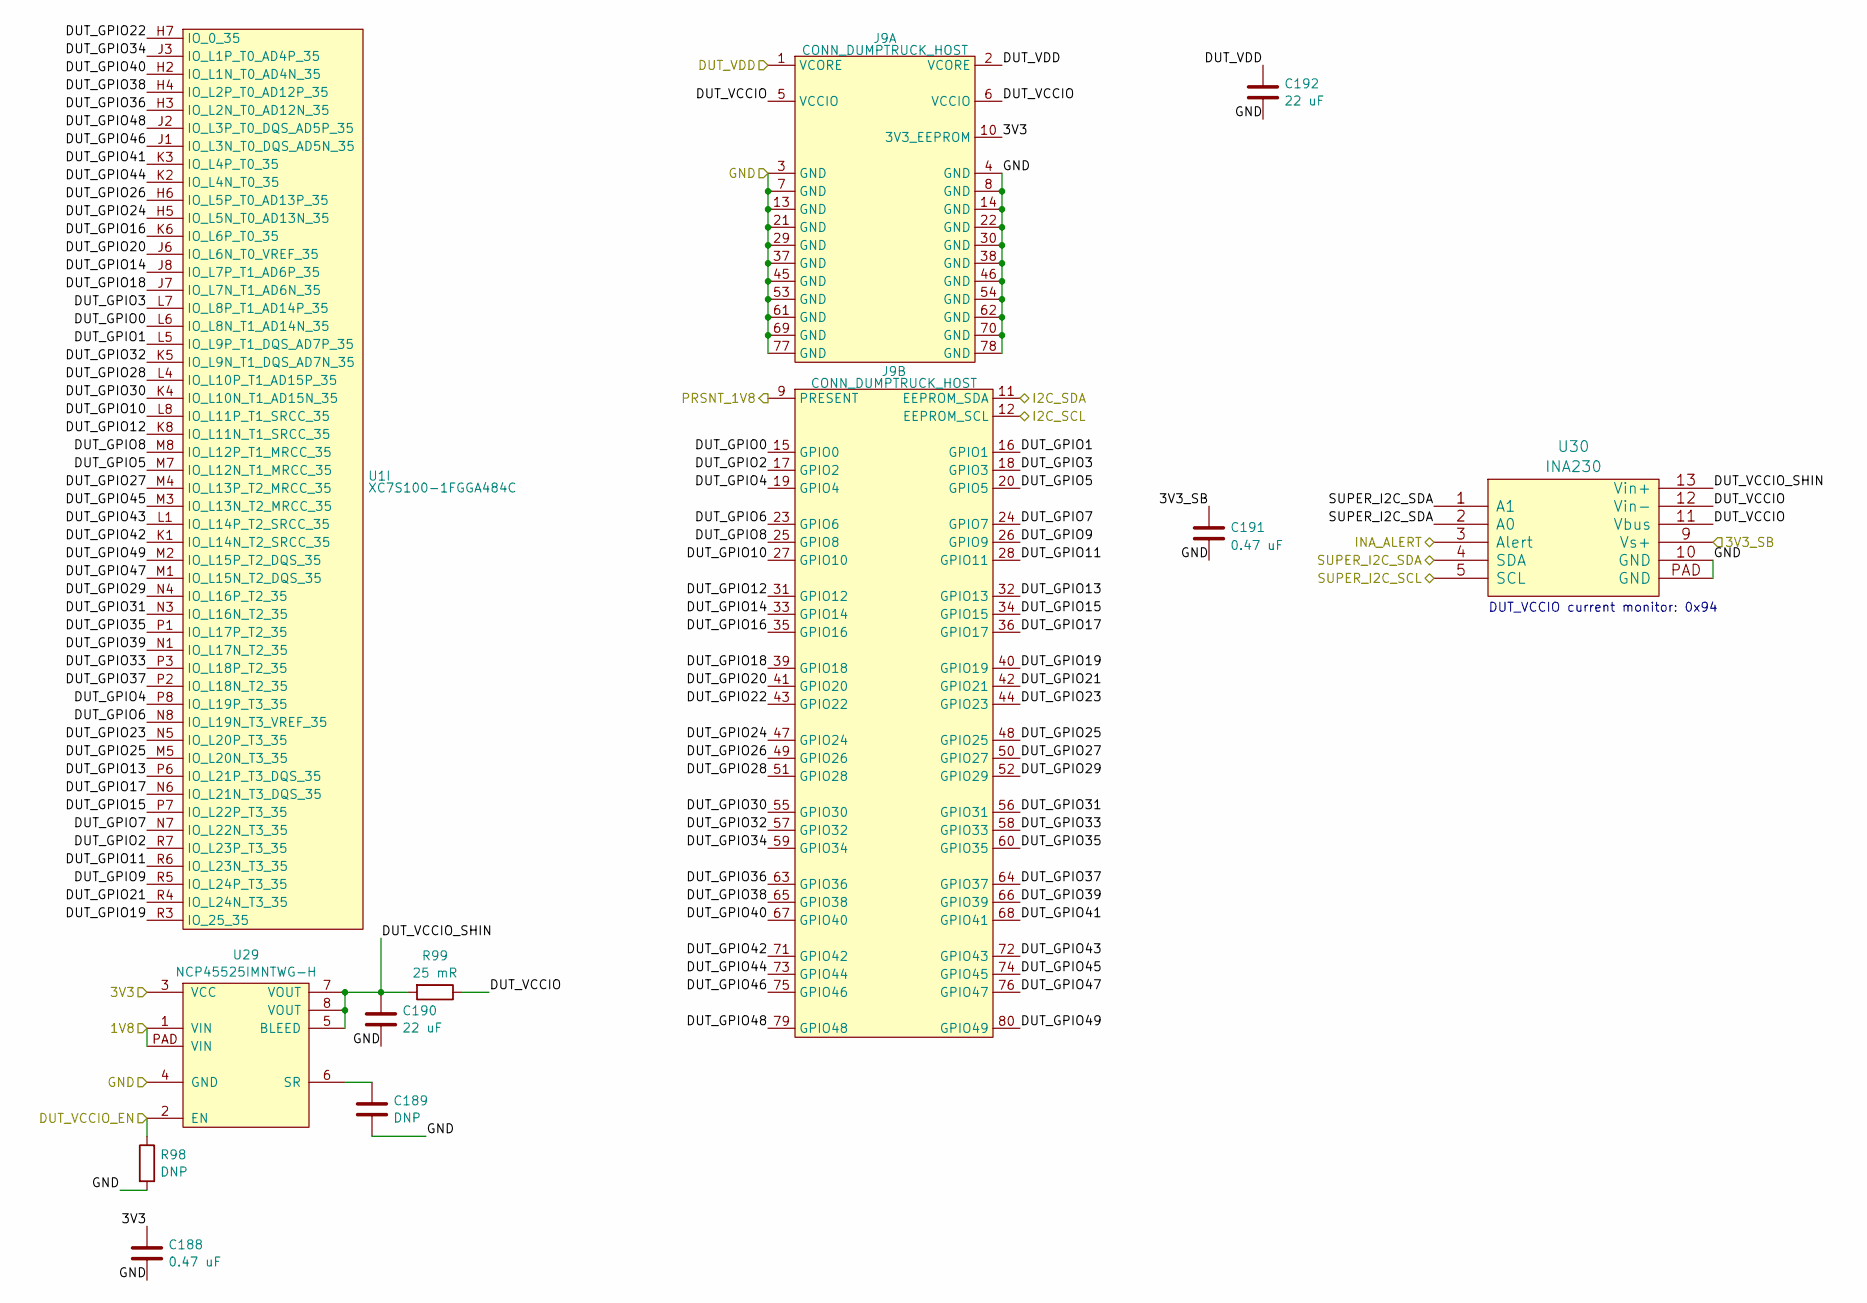
[picture p31: schematic 1v8_vccio.kicad_sch, DUMPTRUCK flash dumper]

Parts:
C188, C191: 0.47 uF; EIA_0402_CAP_NOSILK
C189: DNP; EIA_0402_CAP_NOSILK
C190: 22 uF; EIA_0805_CAP_NOSILK
C192: 22 uF; EIA_1206_CAP_NOSILK
J9: CONN_DUMPTRUCK_HOST; CONN_SAMTEC_BTE-040-01-F-D-A-K
R98: DNP; EIA_0402_RES_NOSILK
R99: 25 mR; EIA_0402_RES_NOSILK
U1: XC7S100-1FGGA484C; BGA_484_22x22_FULLARRAY_1MM
U29: NCP45525IMNTWG-H; DFN_8_0.5MM_2x2MM
U30: INA230; QFN_16_0.5MM_3x3MM

Connections:
/1V8: U29.1 (VIN), U29.PAD (VIN); also elsewhere on the board
/1V8 VCCIO socket/DUT_GPIO0: J9.15 (GPIO0), U1.L6 (IO_L8N_T1_AD14N_35)
/1V8 VCCIO socket/DUT_GPIO1: J9.16 (GPIO1), U1.L5 (IO_L9P_T1_DQS_AD7P_35)
/1V8 VCCIO socket/DUT_GPIO2: J9.17 (GPIO2), U1.R7 (IO_L23P_T3_35)
/1V8 VCCIO socket/DUT_GPIO3: J9.18 (GPIO3), U1.L7 (IO_L8P_T1_AD14P_35)
/1V8 VCCIO socket/DUT_GPIO4: J9.19 (GPIO4), U1.P8 (IO_L19P_T3_35)
/1V8 VCCIO socket/DUT_GPIO5: J9.20 (GPIO5), U1.M7 (IO_L12N_T1_MRCC_35)
/1V8 VCCIO socket/DUT_GPIO6: J9.23 (GPIO6), U1.N8 (IO_L19N_T3_VREF_35)
/1V8 VCCIO socket/DUT_GPIO7: J9.24 (GPIO7), U1.N7 (IO_L22N_T3_35)
/1V8 VCCIO socket/DUT_GPIO8: J9.25 (GPIO8), U1.M8 (IO_L12P_T1_MRCC_35)
/1V8 VCCIO socket/DUT_GPIO9: J9.26 (GPIO9), U1.R5 (IO_L24P_T3_35)
/1V8 VCCIO socket/DUT_GPIO10: J9.27 (GPIO10), U1.L8 (IO_L11P_T1_SRCC_35)
/1V8 VCCIO socket/DUT_GPIO11: J9.28 (GPIO11), U1.R6 (IO_L23N_T3_35)
/1V8 VCCIO socket/DUT_GPIO12: J9.31 (GPIO12), U1.K8 (IO_L11N_T1_SRCC_35)
/1V8 VCCIO socket/DUT_GPIO13: J9.32 (GPIO13), U1.P6 (IO_L21P_T3_DQS_35)
/1V8 VCCIO socket/DUT_GPIO14: J9.33 (GPIO14), U1.J8 (IO_L7P_T1_AD6P_35)
/1V8 VCCIO socket/DUT_GPIO15: J9.34 (GPIO15), U1.P7 (IO_L22P_T3_35)
/1V8 VCCIO socket/DUT_GPIO16: J9.35 (GPIO16), U1.K6 (IO_L6P_T0_35)
/1V8 VCCIO socket/DUT_GPIO17: J9.36 (GPIO17), U1.N6 (IO_L21N_T3_DQS_35)
/1V8 VCCIO socket/DUT_GPIO18: J9.39 (GPIO18), U1.J7 (IO_L7N_T1_AD6N_35)
/1V8 VCCIO socket/DUT_GPIO19: J9.40 (GPIO19), U1.R3 (IO_25_35)
/1V8 VCCIO socket/DUT_GPIO20: J9.41 (GPIO20), U1.J6 (IO_L6N_T0_VREF_35)
/1V8 VCCIO socket/DUT_GPIO21: J9.42 (GPIO21), U1.R4 (IO_L24N_T3_35)
/1V8 VCCIO socket/DUT_GPIO22: J9.43 (GPIO22), U1.H7 (IO_0_35)
/1V8 VCCIO socket/DUT_GPIO23: J9.44 (GPIO23), U1.N5 (IO_L20P_T3_35)
/1V8 VCCIO socket/DUT_GPIO24: J9.47 (GPIO24), U1.H5 (IO_L5N_T0_AD13N_35)
/1V8 VCCIO socket/DUT_GPIO25: J9.48 (GPIO25), U1.M5 (IO_L20N_T3_35)
/1V8 VCCIO socket/DUT_GPIO26: J9.49 (GPIO26), U1.H6 (IO_L5P_T0_AD13P_35)
/1V8 VCCIO socket/DUT_GPIO27: J9.50 (GPIO27), U1.M4 (IO_L13P_T2_MRCC_35)
/1V8 VCCIO socket/DUT_GPIO28: J9.51 (GPIO28), U1.L4 (IO_L10P_T1_AD15P_35)
/1V8 VCCIO socket/DUT_GPIO29: J9.52 (GPIO29), U1.N4 (IO_L16P_T2_35)
/1V8 VCCIO socket/DUT_GPIO30: J9.55 (GPIO30), U1.K4 (IO_L10N_T1_AD15N_35)
/1V8 VCCIO socket/DUT_GPIO31: J9.56 (GPIO31), U1.N3 (IO_L16N_T2_35)
/1V8 VCCIO socket/DUT_GPIO32: J9.57 (GPIO32), U1.K5 (IO_L9N_T1_DQS_AD7N_35)
/1V8 VCCIO socket/DUT_GPIO33: J9.58 (GPIO33), U1.P3 (IO_L18P_T2_35)
/1V8 VCCIO socket/DUT_GPIO34: J9.59 (GPIO34), U1.J3 (IO_L1P_T0_AD4P_35)
/1V8 VCCIO socket/DUT_GPIO35: J9.60 (GPIO35), U1.P1 (IO_L17P_T2_35)
/1V8 VCCIO socket/DUT_GPIO36: J9.63 (GPIO36), U1.H3 (IO_L2N_T0_AD12N_35)
/1V8 VCCIO socket/DUT_GPIO37: J9.64 (GPIO37), U1.P2 (IO_L18N_T2_35)
/1V8 VCCIO socket/DUT_GPIO38: J9.65 (GPIO38), U1.H4 (IO_L2P_T0_AD12P_35)
/1V8 VCCIO socket/DUT_GPIO39: J9.66 (GPIO39), U1.N1 (IO_L17N_T2_35)
/1V8 VCCIO socket/DUT_GPIO40: J9.67 (GPIO40), U1.H2 (IO_L1N_T0_AD4N_35)
/1V8 VCCIO socket/DUT_GPIO41: J9.68 (GPIO41), U1.K3 (IO_L4P_T0_35)
/1V8 VCCIO socket/DUT_GPIO42: J9.71 (GPIO42), U1.K1 (IO_L14N_T2_SRCC_35)
/1V8 VCCIO socket/DUT_GPIO43: J9.72 (GPIO43), U1.L1 (IO_L14P_T2_SRCC_35)
/1V8 VCCIO socket/DUT_GPIO44: J9.73 (GPIO44), U1.K2 (IO_L4N_T0_35)
/1V8 VCCIO socket/DUT_GPIO45: J9.74 (GPIO45), U1.M3 (IO_L13N_T2_MRCC_35)
/1V8 VCCIO socket/DUT_GPIO46: J9.75 (GPIO46), U1.J1 (IO_L3N_T0_DQS_AD5N_35)
/1V8 VCCIO socket/DUT_GPIO47: J9.76 (GPIO47), U1.M1 (IO_L15N_T2_DQS_35)
/1V8 VCCIO socket/DUT_GPIO48: J9.79 (GPIO48), U1.J2 (IO_L3P_T0_DQS_AD5P_35)
/1V8 VCCIO socket/DUT_GPIO49: J9.80 (GPIO49), U1.M2 (IO_L15P_T2_DQS_35)
/1V8 VCCIO socket/DUT_VCCIO: J9.5 (VCCIO), J9.6 (VCCIO), R99.1, U30.11 (Vbus), U30.12 (Vin-)
/1V8 VCCIO socket/DUT_VCCIO_SHIN: C190.1, R99.2, U29.5 (BLEED), U29.7 (VOUT), U29.8 (VOUT), U30.13 (Vin+)
/3V3: C188.1, J9.10 (3V3_EEPROM), U29.3 (VCC); also elsewhere on the board
/3V3_SB: C191.1, U30.9 (Vs+); also elsewhere on the board
/DUT_VCCIO_EN: R98.1, U29.2 (EN); also elsewhere on the board
/DUT_VDD: C192.1, J9.1 (VCORE), J9.2 (VCORE); also elsewhere on the board
/GND: C188.2, C189.2, C190.2, C191.2, C192.2, J9.3 (GND), J9.4 (GND), J9.7 (GND), J9.8 (GND), J9.13 (GND), J9.14 (GND), J9.21 (GND), J9.22 (GND), J9.29 (GND), J9.30 (GND), J9.37 (GND), J9.38 (GND), J9.45 (GND), J9.46 (GND), J9.53 (GND), J9.54 (GND), J9.61 (GND), J9.62 (GND), J9.69 (GND), J9.70 (GND), J9.77 (GND), J9.78 (GND), R98.2, U29.4 (GND), U30.10 (GND), U30.PAD (GND); also elsewhere on the board
/I2C_SCL: J9.12 (EEPROM_SCL); also elsewhere on the board
/I2C_SDA: J9.11 (EEPROM_SDA); also elsewhere on the board
/INA_ALERT: U30.3 (Alert); also elsewhere on the board
/PRSNT_1V8: J9.9 (PRESENT); also elsewhere on the board
/SUPER_I2C_SCL: U30.5 (SCL); also elsewhere on the board
/SUPER_I2C_SDA: U30.1 (A1), U30.2 (A0), U30.4 (SDA); also elsewhere on the board
unnamed: C189.1, U29.6 (SR)

Notes on the sheet:
DUT_VCCIO current monitor: 0x94

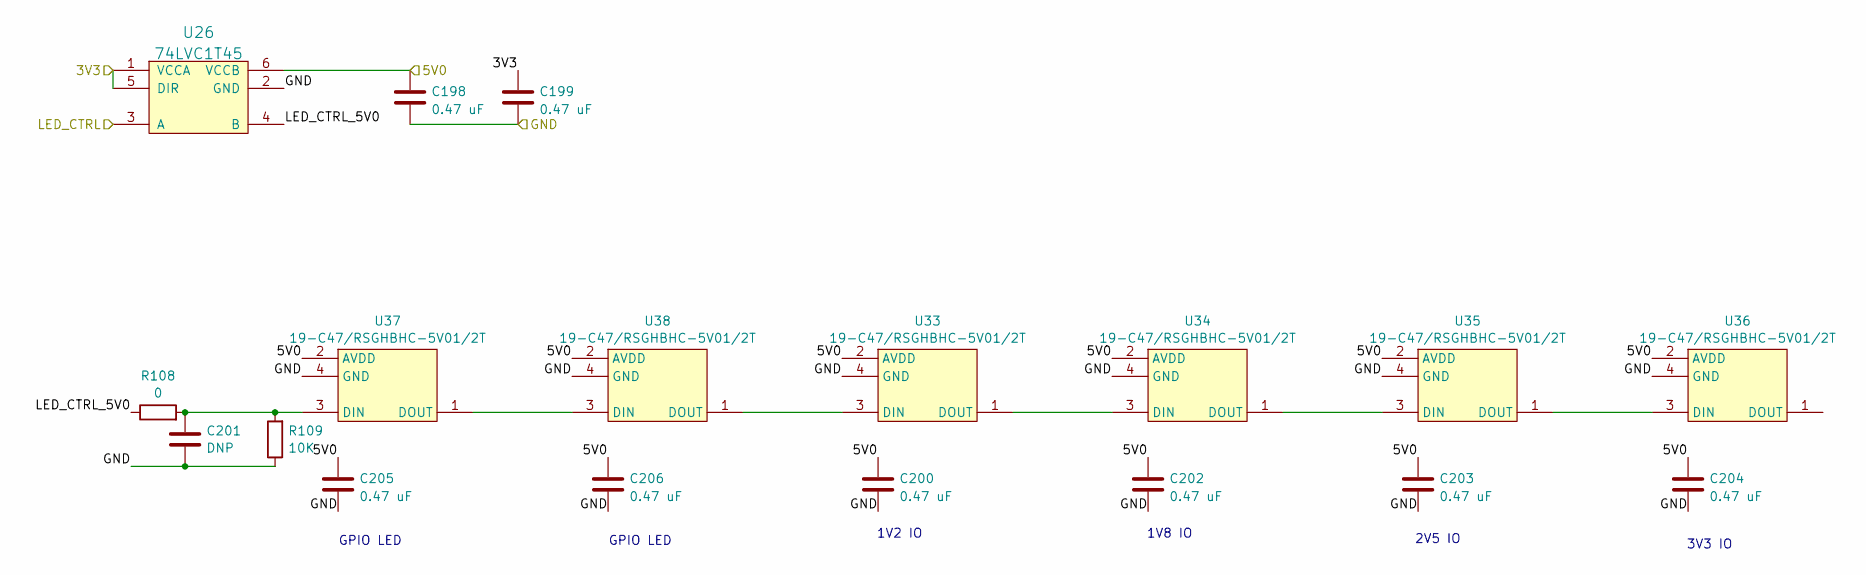
[picture p32: schematic rgb.kicad_sch, DUMPTRUCK flash dumper]

Parts:
C198, C199, C200, C202, C203, C204, C205, C206: 0.47 uF; EIA_0402_CAP_NOSILK
C201: DNP; EIA_0402_CAP_NOSILK
R108: 0; EIA_0402_RES_NOSILK
R109: 10K; EIA_0402_RES_NOSILK
U26: 74LVC1T45; DFN_6_0.5MM_1.6x1.6MM_TI_DPK
U33, U34, U35, U36, U37, U38: 19-C47/RSGHBHC-5V01/2T; LED_EVERLIGHT_19-C47_RSGHBHC-5V01_2T

Connections:
/3V3: C199.1, U26.1 (VCCA), U26.5 (DIR); also elsewhere on the board
/GND: C198.2, C199.2, C200.2, C201.2, C202.2, C203.2, C204.2, C205.2, C206.2, R109.1, U26.2 (GND), U33.4 (GND), U34.4 (GND), U35.4 (GND), U36.4 (GND), U37.4 (GND), U38.4 (GND); also elsewhere on the board
/LED_CTRL: U26.3 (A); also elsewhere on the board
/RGB LEDs/LED_CTRL_5V0: R108.1, U26.4 (B)
/VBUS_SHOUT: C198.1, C200.1, C202.1, C203.1, C204.1, C205.1, C206.1, U26.6 (VCCB), U33.2 (AVDD), U34.2 (AVDD), U35.2 (AVDD), U36.2 (AVDD), U37.2 (AVDD), U38.2 (AVDD); also elsewhere on the board
unnamed: U33.3 (DIN), U38.1 (DOUT)
unnamed: U33.1 (DOUT), U34.3 (DIN)
unnamed: U34.1 (DOUT), U35.3 (DIN)
unnamed: U35.1 (DOUT), U36.3 (DIN)
unnamed: C201.1, R108.2, R109.2, U37.3 (DIN)
unnamed: U37.1 (DOUT), U38.3 (DIN)

Notes on the sheet:
1V2 IO
GPIO LED
2V5 IO
1V8 IO
3V3 IO

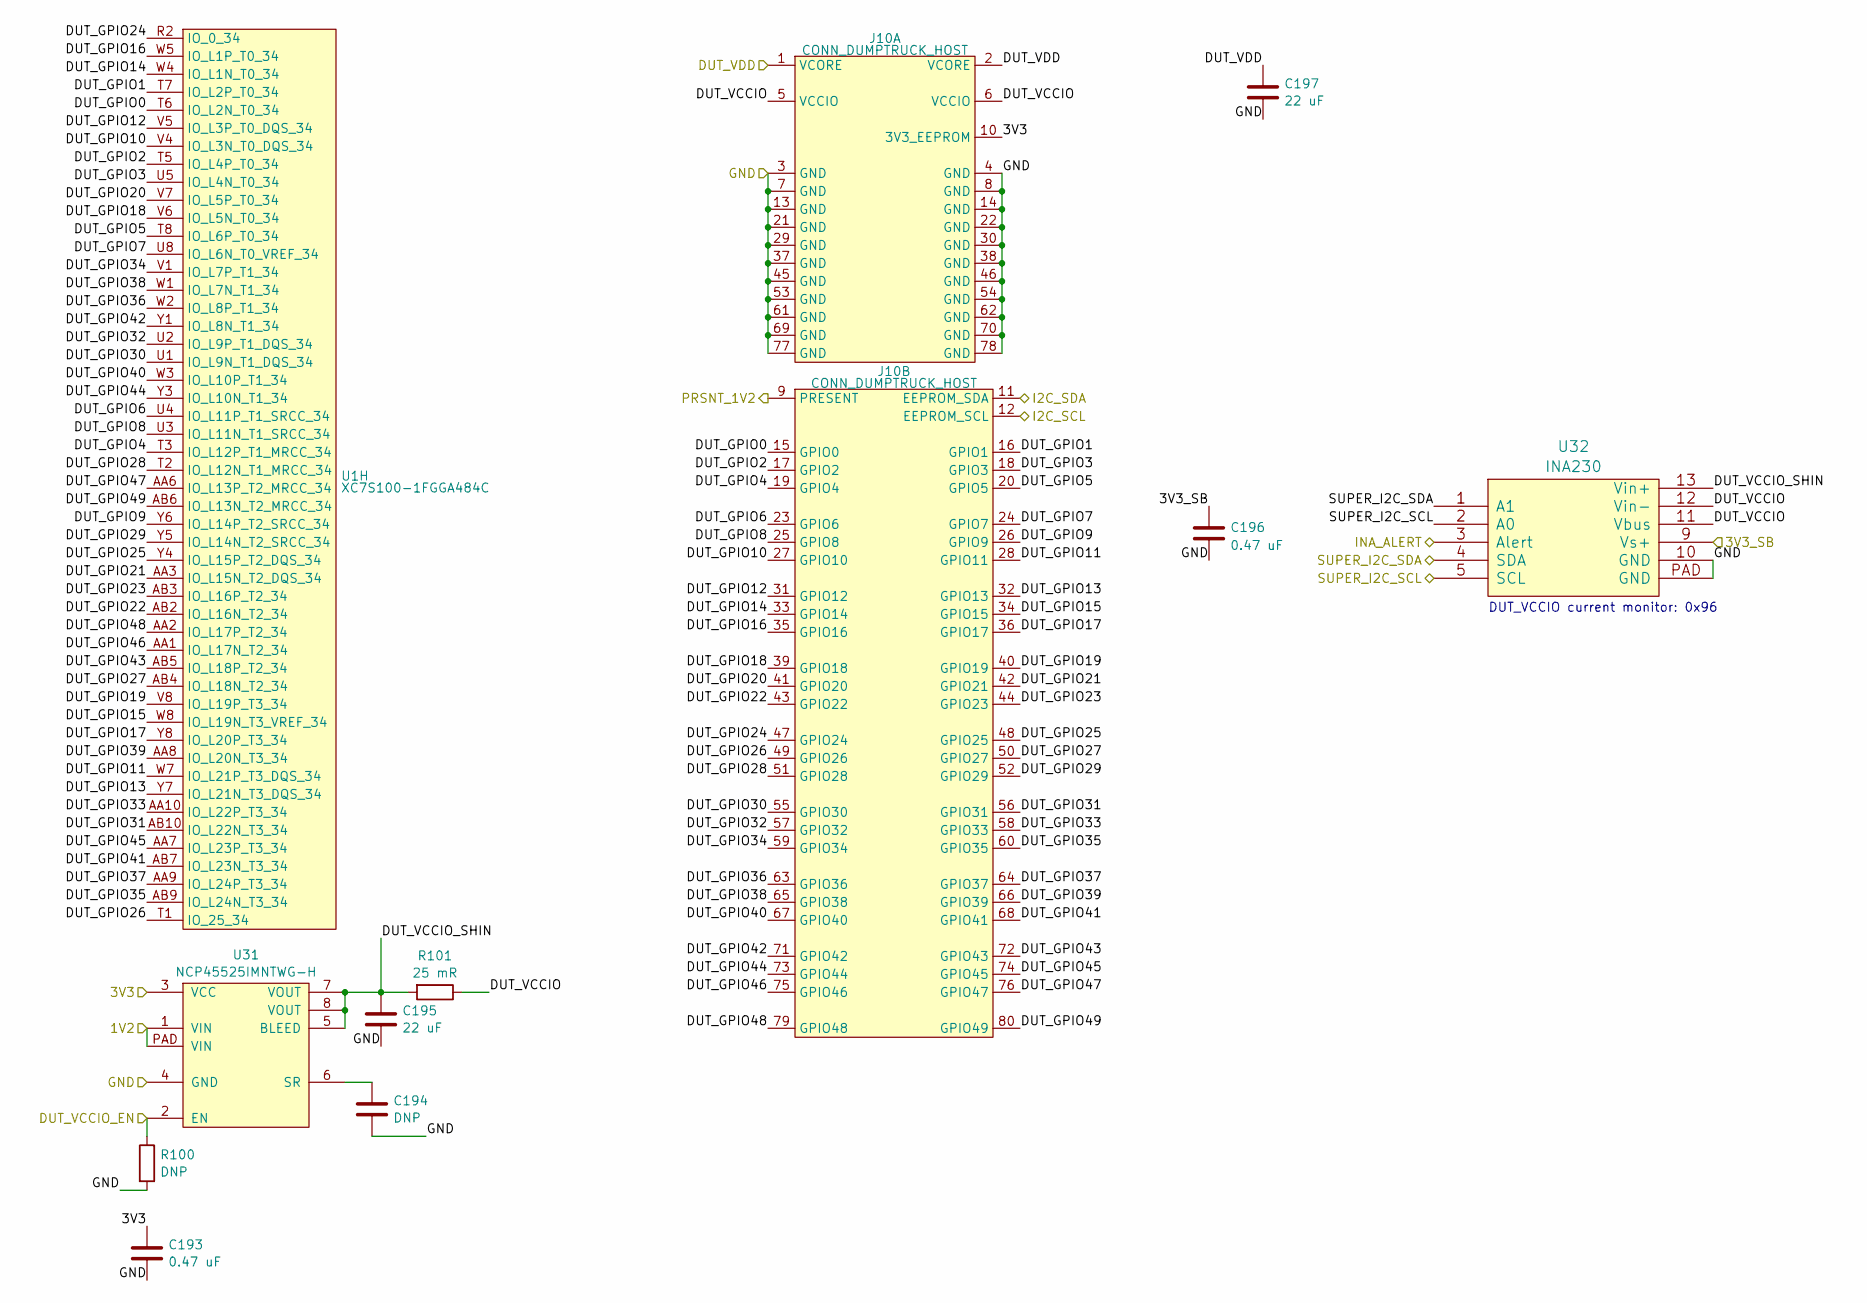
[picture p33: schematic 1v2_vccio.kicad_sch, DUMPTRUCK flash dumper]

Parts:
C193, C196: 0.47 uF; EIA_0402_CAP_NOSILK
C194: DNP; EIA_0402_CAP_NOSILK
C195: 22 uF; EIA_0805_CAP_NOSILK
C197: 22 uF; EIA_1206_CAP_NOSILK
J10: CONN_DUMPTRUCK_HOST; CONN_SAMTEC_BTE-040-01-F-D-A-K
R100: DNP; EIA_0402_RES_NOSILK
R101: 25 mR; EIA_0402_RES_NOSILK
U1: XC7S100-1FGGA484C; BGA_484_22x22_FULLARRAY_1MM
U31: NCP45525IMNTWG-H; DFN_8_0.5MM_2x2MM
U32: INA230; QFN_16_0.5MM_3x3MM

Connections:
/1V2: U31.1 (VIN), U31.PAD (VIN); also elsewhere on the board
/1V2 VCCIO socket/DUT_GPIO0: J10.15 (GPIO0), U1.T6 (IO_L2N_T0_34)
/1V2 VCCIO socket/DUT_GPIO1: J10.16 (GPIO1), U1.T7 (IO_L2P_T0_34)
/1V2 VCCIO socket/DUT_GPIO2: J10.17 (GPIO2), U1.T5 (IO_L4P_T0_34)
/1V2 VCCIO socket/DUT_GPIO3: J10.18 (GPIO3), U1.U5 (IO_L4N_T0_34)
/1V2 VCCIO socket/DUT_GPIO4: J10.19 (GPIO4), U1.T3 (IO_L12P_T1_MRCC_34)
/1V2 VCCIO socket/DUT_GPIO5: J10.20 (GPIO5), U1.T8 (IO_L6P_T0_34)
/1V2 VCCIO socket/DUT_GPIO6: J10.23 (GPIO6), U1.U4 (IO_L11P_T1_SRCC_34)
/1V2 VCCIO socket/DUT_GPIO7: J10.24 (GPIO7), U1.U8 (IO_L6N_T0_VREF_34)
/1V2 VCCIO socket/DUT_GPIO8: J10.25 (GPIO8), U1.U3 (IO_L11N_T1_SRCC_34)
/1V2 VCCIO socket/DUT_GPIO9: J10.26 (GPIO9), U1.Y6 (IO_L14P_T2_SRCC_34)
/1V2 VCCIO socket/DUT_GPIO10: J10.27 (GPIO10), U1.V4 (IO_L3N_T0_DQS_34)
/1V2 VCCIO socket/DUT_GPIO11: J10.28 (GPIO11), U1.W7 (IO_L21P_T3_DQS_34)
/1V2 VCCIO socket/DUT_GPIO12: J10.31 (GPIO12), U1.V5 (IO_L3P_T0_DQS_34)
/1V2 VCCIO socket/DUT_GPIO13: J10.32 (GPIO13), U1.Y7 (IO_L21N_T3_DQS_34)
/1V2 VCCIO socket/DUT_GPIO14: J10.33 (GPIO14), U1.W4 (IO_L1N_T0_34)
/1V2 VCCIO socket/DUT_GPIO15: J10.34 (GPIO15), U1.W8 (IO_L19N_T3_VREF_34)
/1V2 VCCIO socket/DUT_GPIO16: J10.35 (GPIO16), U1.W5 (IO_L1P_T0_34)
/1V2 VCCIO socket/DUT_GPIO17: J10.36 (GPIO17), U1.Y8 (IO_L20P_T3_34)
/1V2 VCCIO socket/DUT_GPIO18: J10.39 (GPIO18), U1.V6 (IO_L5N_T0_34)
/1V2 VCCIO socket/DUT_GPIO19: J10.40 (GPIO19), U1.V8 (IO_L19P_T3_34)
/1V2 VCCIO socket/DUT_GPIO20: J10.41 (GPIO20), U1.V7 (IO_L5P_T0_34)
/1V2 VCCIO socket/DUT_GPIO21: J10.42 (GPIO21), U1.AA3 (IO_L15N_T2_DQS_34)
/1V2 VCCIO socket/DUT_GPIO22: J10.43 (GPIO22), U1.AB2 (IO_L16N_T2_34)
/1V2 VCCIO socket/DUT_GPIO23: J10.44 (GPIO23), U1.AB3 (IO_L16P_T2_34)
/1V2 VCCIO socket/DUT_GPIO24: J10.47 (GPIO24), U1.R2 (IO_0_34)
/1V2 VCCIO socket/DUT_GPIO25: J10.48 (GPIO25), U1.Y4 (IO_L15P_T2_DQS_34)
/1V2 VCCIO socket/DUT_GPIO26: J10.49 (GPIO26), U1.T1 (IO_25_34)
/1V2 VCCIO socket/DUT_GPIO27: J10.50 (GPIO27), U1.AB4 (IO_L18N_T2_34)
/1V2 VCCIO socket/DUT_GPIO28: J10.51 (GPIO28), U1.T2 (IO_L12N_T1_MRCC_34)
/1V2 VCCIO socket/DUT_GPIO29: J10.52 (GPIO29), U1.Y5 (IO_L14N_T2_SRCC_34)
/1V2 VCCIO socket/DUT_GPIO30: J10.55 (GPIO30), U1.U1 (IO_L9N_T1_DQS_34)
/1V2 VCCIO socket/DUT_GPIO31: J10.56 (GPIO31), U1.AB10 (IO_L22N_T3_34)
/1V2 VCCIO socket/DUT_GPIO32: J10.57 (GPIO32), U1.U2 (IO_L9P_T1_DQS_34)
/1V2 VCCIO socket/DUT_GPIO33: J10.58 (GPIO33), U1.AA10 (IO_L22P_T3_34)
/1V2 VCCIO socket/DUT_GPIO34: J10.59 (GPIO34), U1.V1 (IO_L7P_T1_34)
/1V2 VCCIO socket/DUT_GPIO35: J10.60 (GPIO35), U1.AB9 (IO_L24N_T3_34)
/1V2 VCCIO socket/DUT_GPIO36: J10.63 (GPIO36), U1.W2 (IO_L8P_T1_34)
/1V2 VCCIO socket/DUT_GPIO37: J10.64 (GPIO37), U1.AA9 (IO_L24P_T3_34)
/1V2 VCCIO socket/DUT_GPIO38: J10.65 (GPIO38), U1.W1 (IO_L7N_T1_34)
/1V2 VCCIO socket/DUT_GPIO39: J10.66 (GPIO39), U1.AA8 (IO_L20N_T3_34)
/1V2 VCCIO socket/DUT_GPIO40: J10.67 (GPIO40), U1.W3 (IO_L10P_T1_34)
/1V2 VCCIO socket/DUT_GPIO41: J10.68 (GPIO41), U1.AB7 (IO_L23N_T3_34)
/1V2 VCCIO socket/DUT_GPIO42: J10.71 (GPIO42), U1.Y1 (IO_L8N_T1_34)
/1V2 VCCIO socket/DUT_GPIO43: J10.72 (GPIO43), U1.AB5 (IO_L18P_T2_34)
/1V2 VCCIO socket/DUT_GPIO44: J10.73 (GPIO44), U1.Y3 (IO_L10N_T1_34)
/1V2 VCCIO socket/DUT_GPIO45: J10.74 (GPIO45), U1.AA7 (IO_L23P_T3_34)
/1V2 VCCIO socket/DUT_GPIO46: J10.75 (GPIO46), U1.AA1 (IO_L17N_T2_34)
/1V2 VCCIO socket/DUT_GPIO47: J10.76 (GPIO47), U1.AA6 (IO_L13P_T2_MRCC_34)
/1V2 VCCIO socket/DUT_GPIO48: J10.79 (GPIO48), U1.AA2 (IO_L17P_T2_34)
/1V2 VCCIO socket/DUT_GPIO49: J10.80 (GPIO49), U1.AB6 (IO_L13N_T2_MRCC_34)
/1V2 VCCIO socket/DUT_VCCIO: J10.5 (VCCIO), J10.6 (VCCIO), R101.1, U32.11 (Vbus), U32.12 (Vin-)
/1V2 VCCIO socket/DUT_VCCIO_SHIN: C195.1, R101.2, U31.5 (BLEED), U31.7 (VOUT), U31.8 (VOUT), U32.13 (Vin+)
/3V3: C193.1, J10.10 (3V3_EEPROM), U31.3 (VCC); also elsewhere on the board
/3V3_SB: C196.1, U32.9 (Vs+); also elsewhere on the board
/DUT_VCCIO_EN: R100.1, U31.2 (EN); also elsewhere on the board
/DUT_VDD: C197.1, J10.1 (VCORE), J10.2 (VCORE); also elsewhere on the board
/GND: C193.2, C194.2, C195.2, C196.2, C197.2, J10.3 (GND), J10.4 (GND), J10.7 (GND), J10.8 (GND), J10.13 (GND), J10.14 (GND), J10.21 (GND), J10.22 (GND), J10.29 (GND), J10.30 (GND), J10.37 (GND), J10.38 (GND), J10.45 (GND), J10.46 (GND), J10.53 (GND), J10.54 (GND), J10.61 (GND), J10.62 (GND), J10.69 (GND), J10.70 (GND), J10.77 (GND), J10.78 (GND), R100.2, U31.4 (GND), U32.10 (GND), U32.PAD (GND); also elsewhere on the board
/I2C_SCL: J10.12 (EEPROM_SCL); also elsewhere on the board
/I2C_SDA: J10.11 (EEPROM_SDA); also elsewhere on the board
/INA_ALERT: U32.3 (Alert); also elsewhere on the board
/PRSNT_1V2: J10.9 (PRESENT); also elsewhere on the board
/SUPER_I2C_SCL: U32.2 (A0), U32.5 (SCL); also elsewhere on the board
/SUPER_I2C_SDA: U32.1 (A1), U32.4 (SDA); also elsewhere on the board
unnamed: C194.1, U31.6 (SR)

Notes on the sheet:
DUT_VCCIO current monitor: 0x96
