azonenberg/dumptruck/main-pcb/main-pcb.kicad_pcb

## KiCad design main-pcb/main-pcb.kicad_pcb (continued)

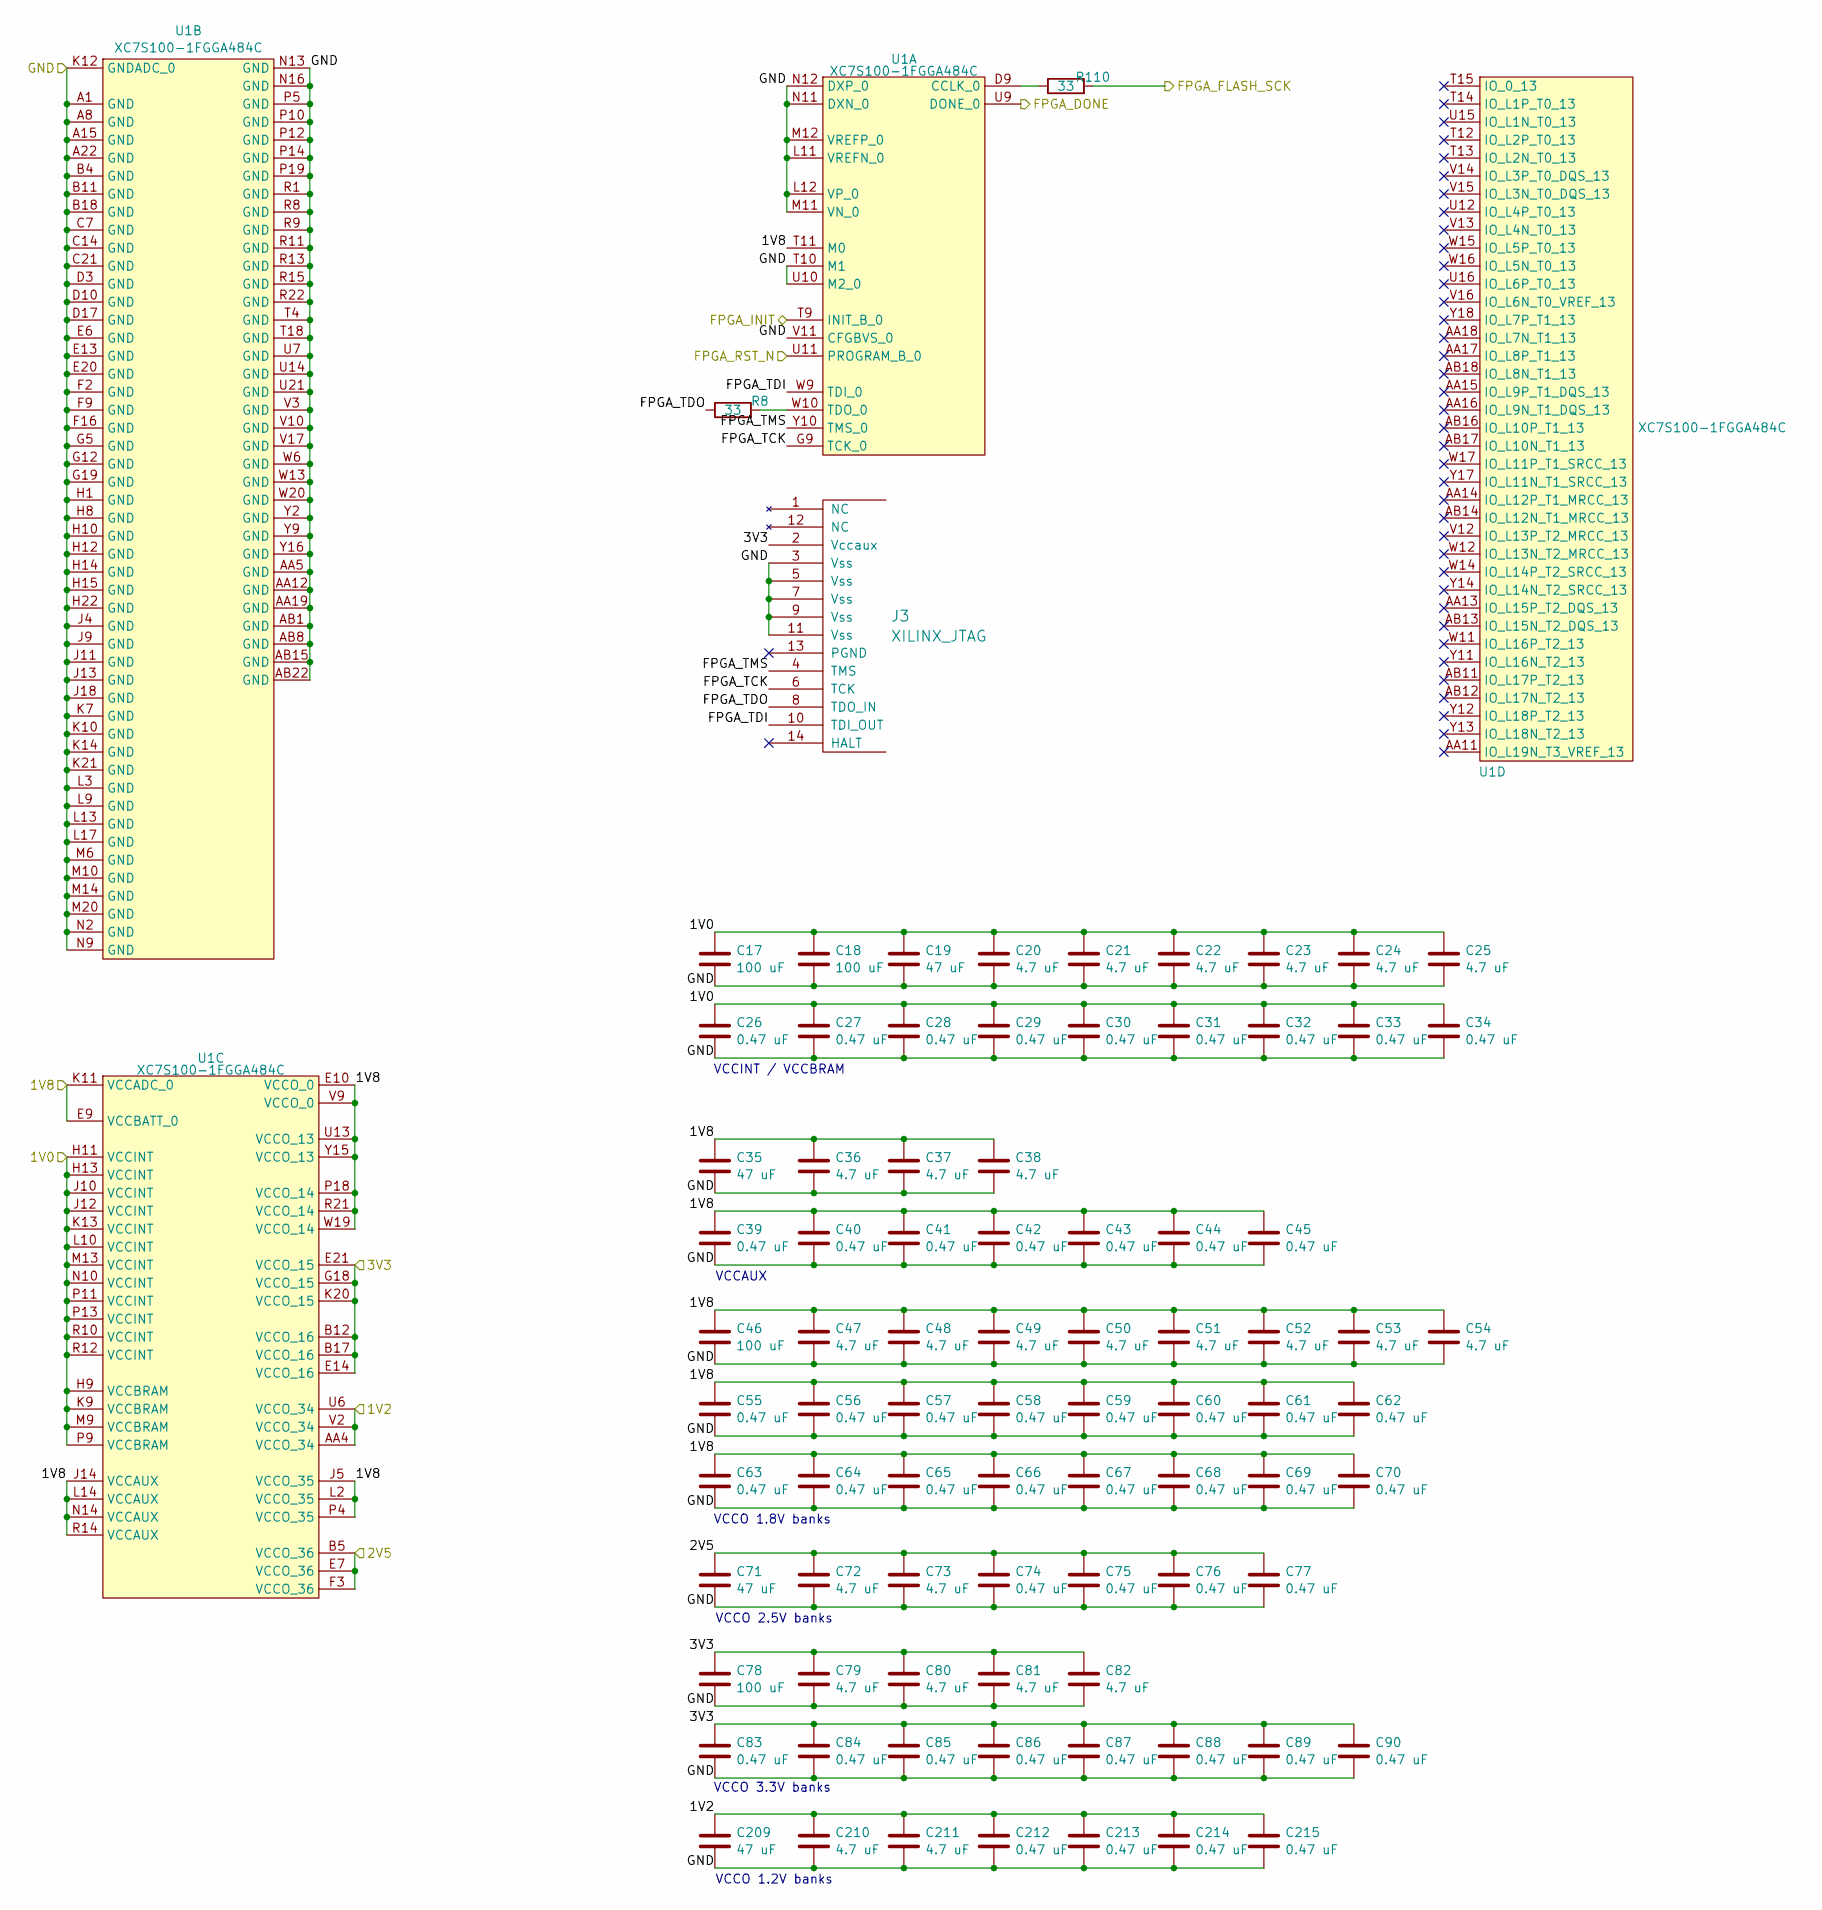
[picture p34: schematic fpgasupport.kicad_sch, DUMPTRUCK flash dumper]

Parts:
C17, C18, C46: 100 uF; EIA_1206_CAP_NOSILK
C19, C35, C71, C209: 47 uF; EIA_1210_CAP_NOSILK
C20, C21, C22, C23, C24, C25, C36, C37, C38, C47, C48, C49, C50, C51, C52, C53, C54, C72, C73, C79, C80, C81, C82, C210, C211: 4.7 uF; EIA_0603_CAP_NOSILK
C26, C27, C28, C29, C30, C31, C32, C33, C34, C39, C40, C41, C42, C43, C44, C45, C55, C56, C57, C58, C59, C60, C61, C62, C63, C64, C65, C66, C67, C68, C69, C70, C74, C75, C76, C77, C83, C84, C85, C86, C87, C88, C89, C90, C212, C213, C214, C215: 0.47 uF; EIA_0402_CAP_NOSILK
C78: 100 uF; EIA_1210_CAP_NOSILK
J3: XILINX_JTAG; XILINX_JTAG_PTH_MOLEX_0878311420
R8, R110: 33; EIA_0402_RES_NOSILK
U1: XC7S100-1FGGA484C; BGA_484_22x22_FULLARRAY_1MM

Connections:
/1V0: C17.1, C18.1, C19.1, C20.1, C21.1, C22.1, C23.1, C24.1, C25.1, C26.1, C27.1, C28.1, C29.1, C30.1, C31.1, C32.1, C33.1, C34.1, U1.H9 (VCCBRAM), U1.H11 (VCCINT), U1.H13 (VCCINT), U1.J10 (VCCINT), U1.J12 (VCCINT), U1.K9 (VCCBRAM), U1.K13 (VCCINT), U1.L10 (VCCINT), U1.M9 (VCCBRAM), U1.M13 (VCCINT), U1.N10 (VCCINT), U1.P9 (VCCBRAM), U1.P11 (VCCINT), U1.P13 (VCCINT), U1.R10 (VCCINT), U1.R12 (VCCINT); also elsewhere on the board
/1V2: C209.1, C210.1, C211.1, C212.1, C213.1, C214.1, C215.1, U1.AA4 (VCCO_34), U1.U6 (VCCO_34), U1.V2 (VCCO_34); also elsewhere on the board
/1V8: C35.1, C36.1, C37.1, C38.1, C39.1, C40.1, C41.1, C42.1, C43.1, C44.1, C45.1, C46.1, C47.1, C48.1, C49.1, C50.1, C51.1, C52.1, C53.1, C54.1, C55.1, C56.1, C57.1, C58.1, C59.1, C60.1, C61.1, C62.1, C63.1, C64.1, C65.1, C66.1, C67.1, C68.1, C69.1, C70.1, U1.E9 (VCCBATT_0), U1.E10 (VCCO_0), U1.J5 (VCCO_35), U1.J14 (VCCAUX), U1.K11 (VCCADC_0), U1.L2 (VCCO_35), U1.L14 (VCCAUX), U1.N14 (VCCAUX), U1.P4 (VCCO_35), U1.P18 (VCCO_14), U1.R14 (VCCAUX), U1.R21 (VCCO_14), U1.T11 (M0), U1.U13 (VCCO_13), U1.V9 (VCCO_0), U1.W19 (VCCO_14), U1.Y15 (VCCO_13); also elsewhere on the board
/2V5: C71.1, C72.1, C73.1, C74.1, C75.1, C76.1, C77.1, U1.B5 (VCCO_36), U1.E7 (VCCO_36), U1.F3 (VCCO_36); also elsewhere on the board
/3V3: C78.1, C79.1, C80.1, C81.1, C82.1, C83.1, C84.1, C85.1, C86.1, C87.1, C88.1, C89.1, C90.1, J3.2 (Vccaux), U1.B12 (VCCO_16), U1.B17 (VCCO_16), U1.E14 (VCCO_16), U1.E21 (VCCO_15), U1.G18 (VCCO_15), U1.K20 (VCCO_15); also elsewhere on the board
/FLASH_SCK: R110.2; also elsewhere on the board
/FPGA support/FPGA_INIT: U1.T9 (INIT_B_0); also elsewhere on the board
/FPGA support/FPGA_RST_N: U1.U11 (PROGRAM_B_0); also elsewhere on the board
/FPGA support/FPGA_TCK: J3.6 (TCK), U1.G9 (TCK_0)
/FPGA support/FPGA_TDI: J3.10 (TDI_OUT), U1.W9 (TDI_0)
/FPGA support/FPGA_TDO: J3.8 (TDO_IN), R8.1
/FPGA support/FPGA_TMS: J3.4 (TMS), U1.Y10 (TMS_0)
/FPGA_DONE: U1.U9 (DONE_0); also elsewhere on the board
/GND: C17.2, C18.2, C19.2, C20.2, C21.2, C22.2, C23.2, C24.2, C25.2, C26.2, C27.2, C28.2, C29.2, C30.2, C31.2, C32.2, C33.2, C34.2, C35.2, C36.2, C37.2, C38.2, C39.2, C40.2, C41.2, C42.2, C43.2, C44.2, C45.2, C46.2, C47.2, C48.2, C49.2, C50.2, C51.2, C52.2, C53.2, C54.2, C55.2, C56.2, C57.2, C58.2, C59.2, C60.2, C61.2, C62.2, C63.2, C64.2, C65.2, C66.2, C67.2, C68.2, C69.2, C70.2, C71.2, C72.2, C73.2, C74.2, C75.2, C76.2, C77.2, C78.2, C79.2, C80.2, C81.2, C82.2, C83.2, C84.2, C85.2, C86.2, C87.2, C88.2, C89.2, C90.2, C209.2, C210.2, C211.2, C212.2, C213.2, C214.2, C215.2, J3.3 (Vss), J3.5 (Vss), J3.7 (Vss), J3.9 (Vss), J3.11 (Vss), U1.A1 (GND), U1.A8 (GND), U1.A15 (GND), U1.A22 (GND), U1.AA5 (GND), U1.AA12 (GND), U1.AA19 (GND), U1.AB1 (GND), U1.AB8 (GND), U1.AB15 (GND), U1.AB22 (GND), U1.B4 (GND), U1.B11 (GND), U1.B18 (GND), U1.C7 (GND), U1.C14 (GND), U1.C21 (GND), U1.D3 (GND), U1.D10 (GND), U1.D17 (GND), U1.E6 (GND), U1.E13 (GND), U1.E20 (GND), U1.F2 (GND), U1.F9 (GND), U1.F16 (GND), U1.G5 (GND), U1.G12 (GND), U1.G19 (GND), U1.H1 (GND), U1.H8 (GND), U1.H10 (GND), U1.H12 (GND), U1.H14 (GND), U1.H15 (GND), U1.H22 (GND), U1.J4 (GND), U1.J9 (GND), U1.J11 (GND), U1.J13 (GND), U1.J18 (GND), U1.K7 (GND), U1.K10 (GND), U1.K12 (GNDADC_0), U1.K14 (GND), U1.K21 (GND), U1.L3 (GND), U1.L9 (GND), U1.L11 (VREFN_0), U1.L12 (VP_0), U1.L13 (GND), U1.L17 (GND), U1.M6 (GND), U1.M10 (GND), U1.M11 (VN_0), U1.M12 (VREFP_0), U1.M14 (GND), U1.M20 (GND), U1.N2 (GND), U1.N9 (GND), U1.N11 (DXN_0), U1.N12 (DXP_0), U1.N13 (GND), U1.N16 (GND), U1.P5 (GND), U1.P10 (GND), U1.P12 (GND), U1.P14 (GND), U1.P19 (GND), U1.R1 (GND), U1.R8 (GND), U1.R9 (GND), U1.R11 (GND), U1.R13 (GND), U1.R15 (GND), U1.R22 (GND), U1.T4 (GND), U1.T10 (M1), U1.T18 (GND), U1.U7 (GND), U1.U10 (M2_0), U1.U14 (GND), U1.U21 (GND), U1.V3 (GND), U1.V10 (GND), U1.V11 (CFGBVS_0), U1.V17 (GND), U1.W6 (GND), U1.W13 (GND), U1.W20 (GND), U1.Y2 (GND), U1.Y9 (GND), U1.Y16 (GND); also elsewhere on the board
unnamed: R110.1, U1.D9 (CCLK_0)
unnamed: R8.2, U1.W10 (TDO_0)

Notes on the sheet:
VCCO 1.2V banks
VCCO 2.5V banks
VCCAUX
VCCO 3.3V banks
VCCINT / VCCBRAM
VCCO 1.8V banks

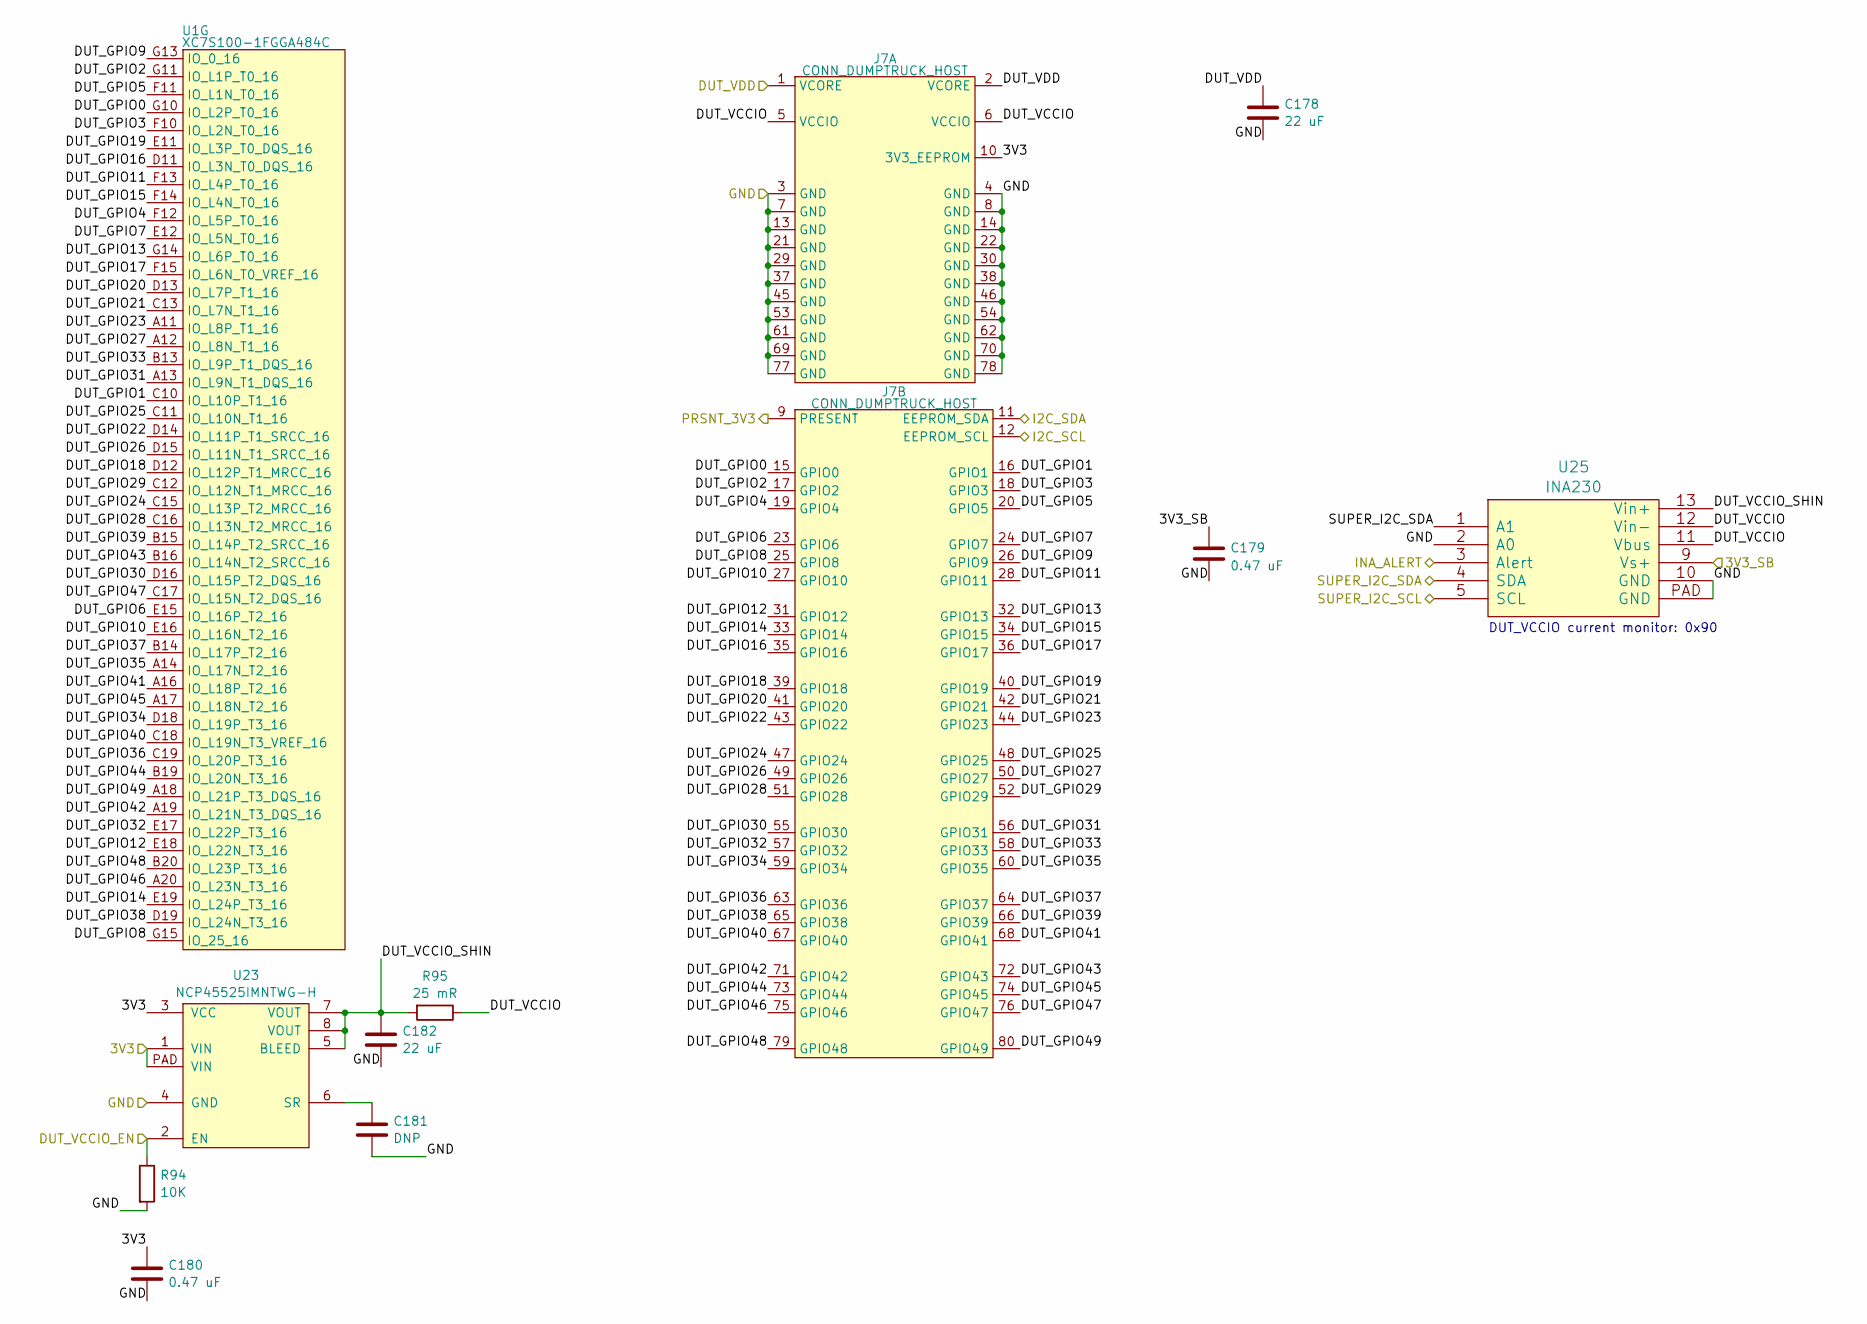
[picture p35: schematic 3v3_vccio.kicad_sch, DUMPTRUCK flash dumper]

Parts:
C178: 22 uF; EIA_1206_CAP_NOSILK
C179, C180: 0.47 uF; EIA_0402_CAP_NOSILK
C181: DNP; EIA_0402_CAP_NOSILK
C182: 22 uF; EIA_1210_CAP_NOSILK
J7: CONN_DUMPTRUCK_HOST; CONN_SAMTEC_BTE-040-01-F-D-A-K
R94: 10K; EIA_0402_RES_NOSILK
R95: 25 mR; EIA_0402_RES_NOSILK
U1: XC7S100-1FGGA484C; BGA_484_22x22_FULLARRAY_1MM
U23: NCP45525IMNTWG-H; DFN_8_0.5MM_2x2MM
U25: INA230; QFN_16_0.5MM_3x3MM

Connections:
/3V3: C180.1, J7.10 (3V3_EEPROM), U23.1 (VIN), U23.3 (VCC), U23.PAD (VIN); also elsewhere on the board
/3V3 VCCIO socket/DUT_GPIO0: J7.15 (GPIO0), U1.G10 (IO_L2P_T0_16)
/3V3 VCCIO socket/DUT_GPIO1: J7.16 (GPIO1), U1.C10 (IO_L10P_T1_16)
/3V3 VCCIO socket/DUT_GPIO2: J7.17 (GPIO2), U1.G11 (IO_L1P_T0_16)
/3V3 VCCIO socket/DUT_GPIO3: J7.18 (GPIO3), U1.F10 (IO_L2N_T0_16)
/3V3 VCCIO socket/DUT_GPIO4: J7.19 (GPIO4), U1.F12 (IO_L5P_T0_16)
/3V3 VCCIO socket/DUT_GPIO5: J7.20 (GPIO5), U1.F11 (IO_L1N_T0_16)
/3V3 VCCIO socket/DUT_GPIO6: J7.23 (GPIO6), U1.E15 (IO_L16P_T2_16)
/3V3 VCCIO socket/DUT_GPIO7: J7.24 (GPIO7), U1.E12 (IO_L5N_T0_16)
/3V3 VCCIO socket/DUT_GPIO8: J7.25 (GPIO8), U1.G15 (IO_25_16)
/3V3 VCCIO socket/DUT_GPIO9: J7.26 (GPIO9), U1.G13 (IO_0_16)
/3V3 VCCIO socket/DUT_GPIO10: J7.27 (GPIO10), U1.E16 (IO_L16N_T2_16)
/3V3 VCCIO socket/DUT_GPIO11: J7.28 (GPIO11), U1.F13 (IO_L4P_T0_16)
/3V3 VCCIO socket/DUT_GPIO12: J7.31 (GPIO12), U1.E18 (IO_L22N_T3_16)
/3V3 VCCIO socket/DUT_GPIO13: J7.32 (GPIO13), U1.G14 (IO_L6P_T0_16)
/3V3 VCCIO socket/DUT_GPIO14: J7.33 (GPIO14), U1.E19 (IO_L24P_T3_16)
/3V3 VCCIO socket/DUT_GPIO15: J7.34 (GPIO15), U1.F14 (IO_L4N_T0_16)
/3V3 VCCIO socket/DUT_GPIO16: J7.35 (GPIO16), U1.D11 (IO_L3N_T0_DQS_16)
/3V3 VCCIO socket/DUT_GPIO17: J7.36 (GPIO17), U1.F15 (IO_L6N_T0_VREF_16)
/3V3 VCCIO socket/DUT_GPIO18: J7.39 (GPIO18), U1.D12 (IO_L12P_T1_MRCC_16)
/3V3 VCCIO socket/DUT_GPIO19: J7.40 (GPIO19), U1.E11 (IO_L3P_T0_DQS_16)
/3V3 VCCIO socket/DUT_GPIO20: J7.41 (GPIO20), U1.D13 (IO_L7P_T1_16)
/3V3 VCCIO socket/DUT_GPIO21: J7.42 (GPIO21), U1.C13 (IO_L7N_T1_16)
/3V3 VCCIO socket/DUT_GPIO22: J7.43 (GPIO22), U1.D14 (IO_L11P_T1_SRCC_16)
/3V3 VCCIO socket/DUT_GPIO23: J7.44 (GPIO23), U1.A11 (IO_L8P_T1_16)
/3V3 VCCIO socket/DUT_GPIO24: J7.47 (GPIO24), U1.C15 (IO_L13P_T2_MRCC_16)
/3V3 VCCIO socket/DUT_GPIO25: J7.48 (GPIO25), U1.C11 (IO_L10N_T1_16)
/3V3 VCCIO socket/DUT_GPIO26: J7.49 (GPIO26), U1.D15 (IO_L11N_T1_SRCC_16)
/3V3 VCCIO socket/DUT_GPIO27: J7.50 (GPIO27), U1.A12 (IO_L8N_T1_16)
/3V3 VCCIO socket/DUT_GPIO28: J7.51 (GPIO28), U1.C16 (IO_L13N_T2_MRCC_16)
/3V3 VCCIO socket/DUT_GPIO29: J7.52 (GPIO29), U1.C12 (IO_L12N_T1_MRCC_16)
/3V3 VCCIO socket/DUT_GPIO30: J7.55 (GPIO30), U1.D16 (IO_L15P_T2_DQS_16)
/3V3 VCCIO socket/DUT_GPIO31: J7.56 (GPIO31), U1.A13 (IO_L9N_T1_DQS_16)
/3V3 VCCIO socket/DUT_GPIO32: J7.57 (GPIO32), U1.E17 (IO_L22P_T3_16)
/3V3 VCCIO socket/DUT_GPIO33: J7.58 (GPIO33), U1.B13 (IO_L9P_T1_DQS_16)
/3V3 VCCIO socket/DUT_GPIO34: J7.59 (GPIO34), U1.D18 (IO_L19P_T3_16)
/3V3 VCCIO socket/DUT_GPIO35: J7.60 (GPIO35), U1.A14 (IO_L17N_T2_16)
/3V3 VCCIO socket/DUT_GPIO36: J7.63 (GPIO36), U1.C19 (IO_L20P_T3_16)
/3V3 VCCIO socket/DUT_GPIO37: J7.64 (GPIO37), U1.B14 (IO_L17P_T2_16)
/3V3 VCCIO socket/DUT_GPIO38: J7.65 (GPIO38), U1.D19 (IO_L24N_T3_16)
/3V3 VCCIO socket/DUT_GPIO39: J7.66 (GPIO39), U1.B15 (IO_L14P_T2_SRCC_16)
/3V3 VCCIO socket/DUT_GPIO40: J7.67 (GPIO40), U1.C18 (IO_L19N_T3_VREF_16)
/3V3 VCCIO socket/DUT_GPIO41: J7.68 (GPIO41), U1.A16 (IO_L18P_T2_16)
/3V3 VCCIO socket/DUT_GPIO42: J7.71 (GPIO42), U1.A19 (IO_L21N_T3_DQS_16)
/3V3 VCCIO socket/DUT_GPIO43: J7.72 (GPIO43), U1.B16 (IO_L14N_T2_SRCC_16)
/3V3 VCCIO socket/DUT_GPIO44: J7.73 (GPIO44), U1.B19 (IO_L20N_T3_16)
/3V3 VCCIO socket/DUT_GPIO45: J7.74 (GPIO45), U1.A17 (IO_L18N_T2_16)
/3V3 VCCIO socket/DUT_GPIO46: J7.75 (GPIO46), U1.A20 (IO_L23N_T3_16)
/3V3 VCCIO socket/DUT_GPIO47: J7.76 (GPIO47), U1.C17 (IO_L15N_T2_DQS_16)
/3V3 VCCIO socket/DUT_GPIO48: J7.79 (GPIO48), U1.B20 (IO_L23P_T3_16)
/3V3 VCCIO socket/DUT_GPIO49: J7.80 (GPIO49), U1.A18 (IO_L21P_T3_DQS_16)
/3V3 VCCIO socket/DUT_VCCIO: J7.5 (VCCIO), J7.6 (VCCIO), R95.1, U25.11 (Vbus), U25.12 (Vin-)
/3V3 VCCIO socket/DUT_VCCIO_SHIN: C182.1, R95.2, U23.5 (BLEED), U23.7 (VOUT), U23.8 (VOUT), U25.13 (Vin+)
/3V3_SB: C179.1, U25.9 (Vs+); also elsewhere on the board
/DUT_VCCIO_EN: R94.1, U23.2 (EN); also elsewhere on the board
/DUT_VDD: C178.1, J7.1 (VCORE), J7.2 (VCORE); also elsewhere on the board
/GND: C178.2, C179.2, C180.2, C181.2, C182.2, J7.3 (GND), J7.4 (GND), J7.7 (GND), J7.8 (GND), J7.13 (GND), J7.14 (GND), J7.21 (GND), J7.22 (GND), J7.29 (GND), J7.30 (GND), J7.37 (GND), J7.38 (GND), J7.45 (GND), J7.46 (GND), J7.53 (GND), J7.54 (GND), J7.61 (GND), J7.62 (GND), J7.69 (GND), J7.70 (GND), J7.77 (GND), J7.78 (GND), R94.2, U23.4 (GND), U25.2 (A0), U25.10 (GND), U25.PAD (GND); also elsewhere on the board
/I2C_SCL: J7.12 (EEPROM_SCL); also elsewhere on the board
/I2C_SDA: J7.11 (EEPROM_SDA); also elsewhere on the board
/INA_ALERT: U25.3 (Alert); also elsewhere on the board
/PRSNT_3V3: J7.9 (PRESENT); also elsewhere on the board
/SUPER_I2C_SCL: U25.5 (SCL); also elsewhere on the board
/SUPER_I2C_SDA: U25.1 (A1), U25.4 (SDA); also elsewhere on the board
unnamed: C181.1, U23.6 (SR)

Notes on the sheet:
DUT_VCCIO current monitor: 0x90

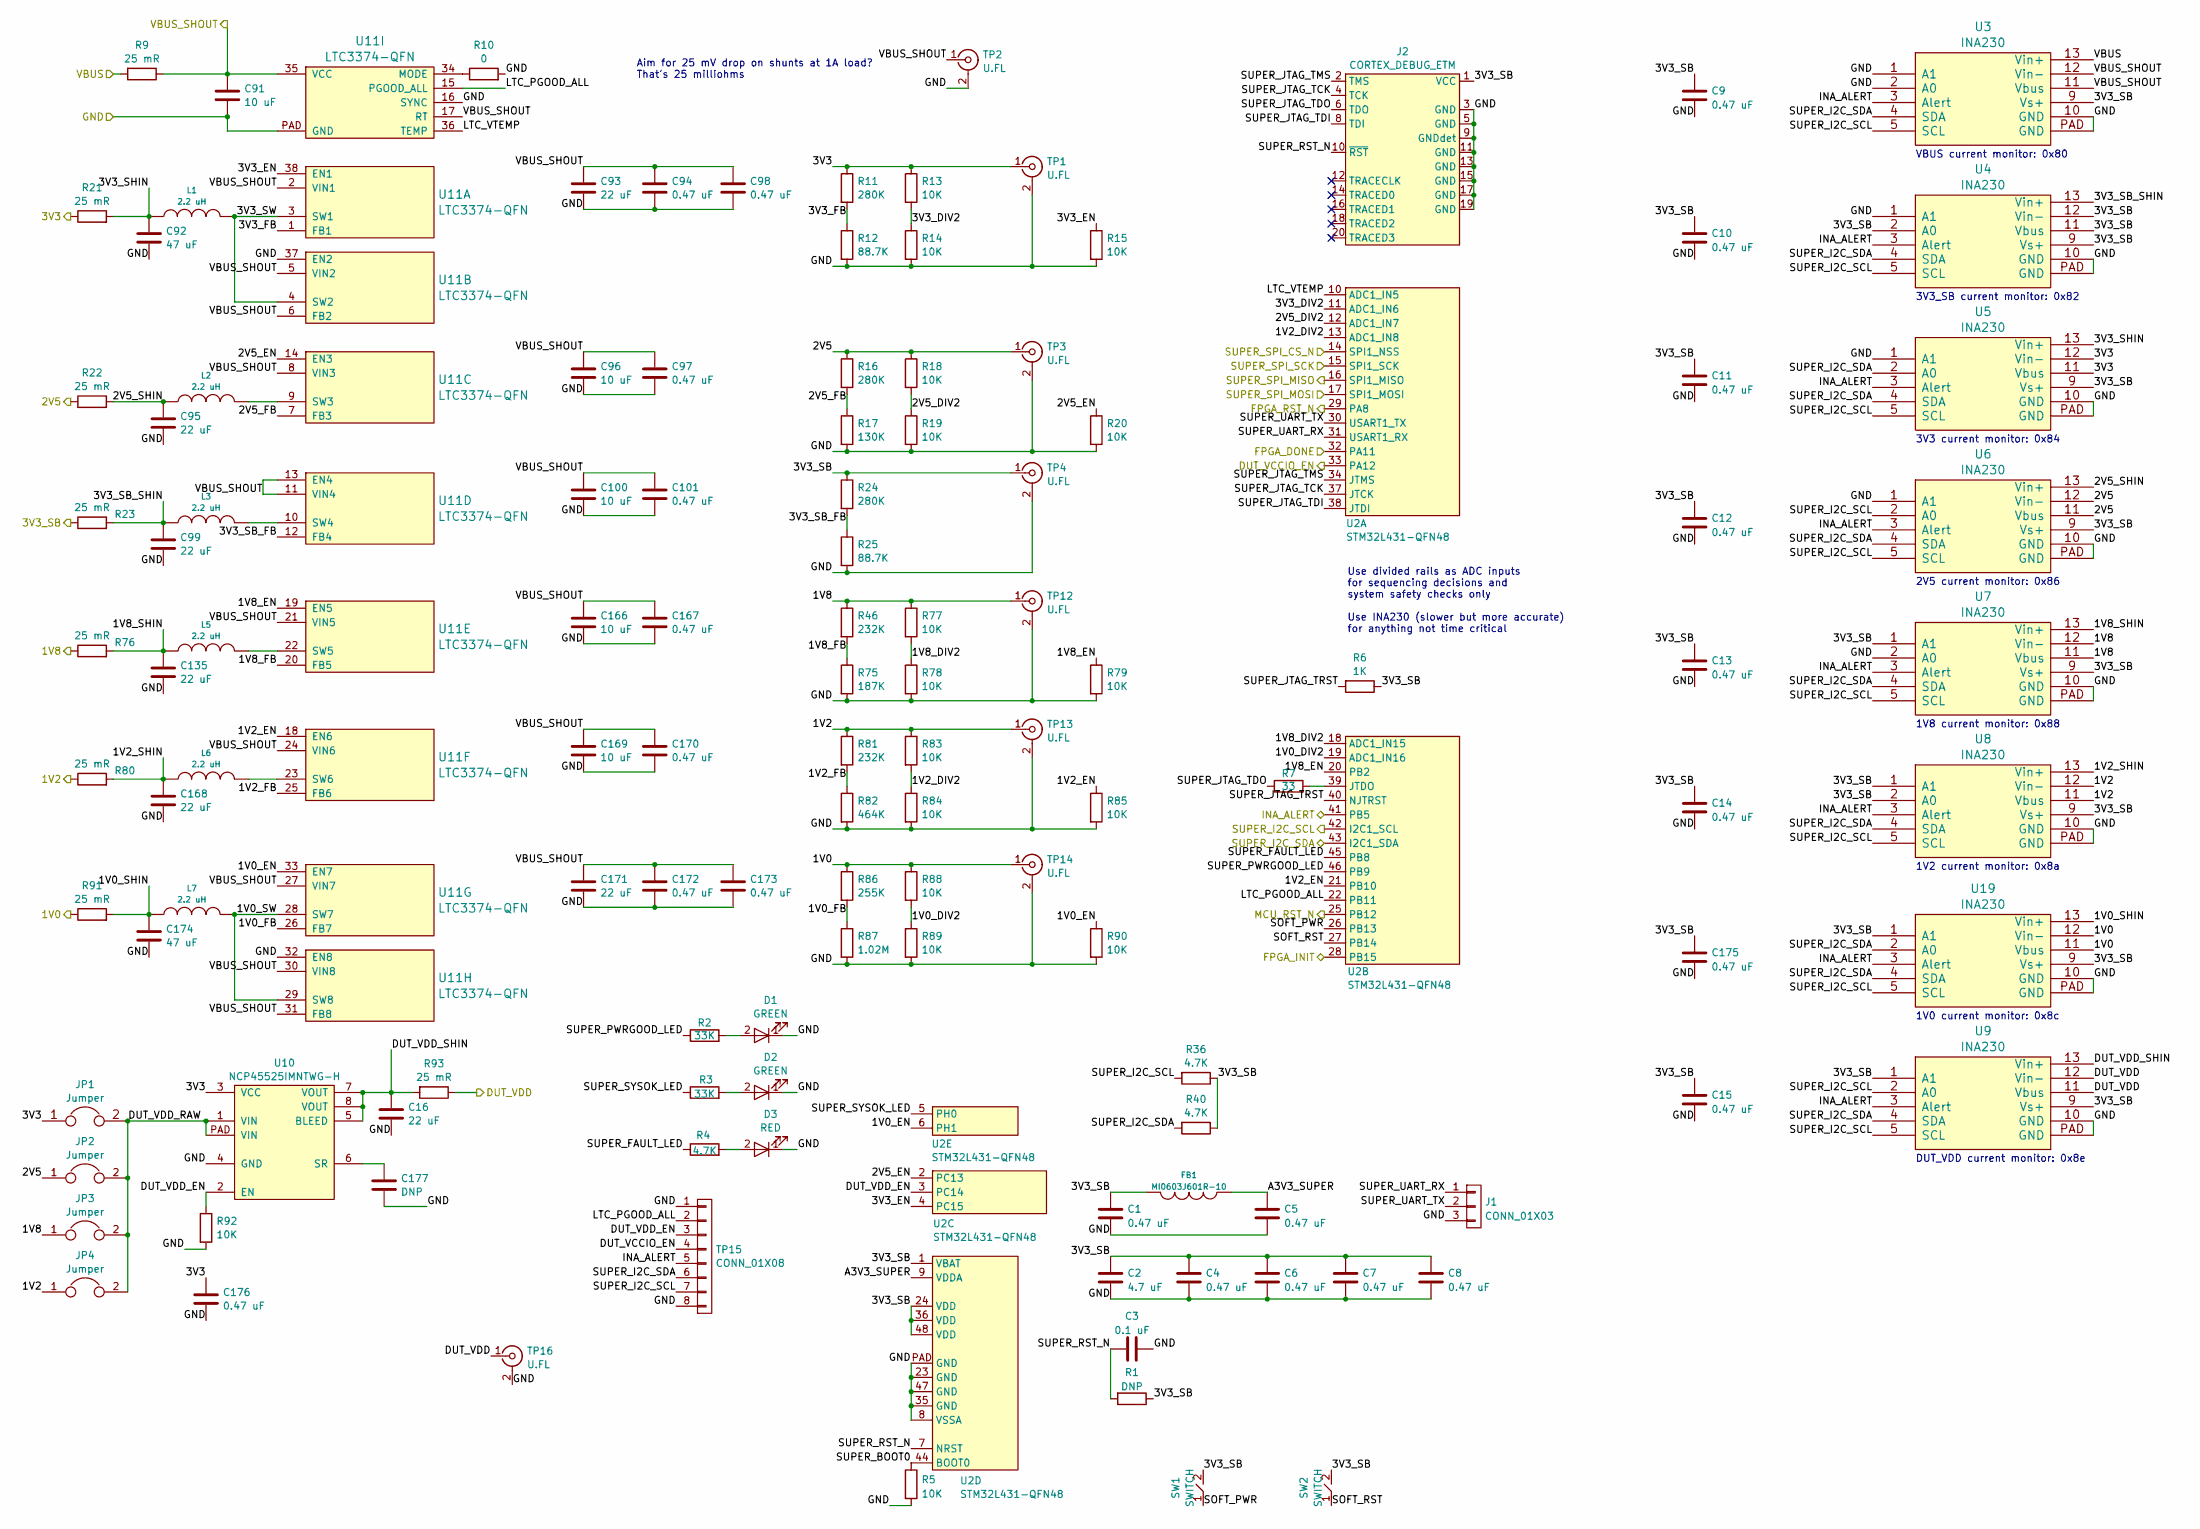
[picture p36: schematic psu.kicad_sch, DUMPTRUCK flash dumper]

Parts:
C1, C4, C5, C6, C7, C8, C9, C10, C11, C12, C13, C14, C15, C94, C97, C98, C101, C167, C170, C172, C173, C175, C176: 0.47 uF; EIA_0402_CAP_NOSILK
C2: 4.7 uF; EIA_0603_CAP_NOSILK
C3: 0.1 uF; EIA_0402_CAP_NOSILK
C16, C93, C99, C171: 22 uF; EIA_1210_CAP_NOSILK
C91, C96: 10 uF; EIA_1210_CAP_NOSILK
C92, C174: 47 uF; EIA_1210_CAP_NOSILK
C95, C135: 22 uF; EIA_1206_CAP_NOSILK
C100, C166, C169: 10 uF; EIA_1206_CAP_NOSILK
C168: 22 uF; EIA_0805_CAP_NOSILK
C177: DNP; EIA_0402_CAP_NOSILK
D1, D2: GREEN; EIA_0402_LED
D3: RED; EIA_0402_LED
FB1: MI0603J601R-10; EIA_0603_INDUCTOR_NOSILK
J1: CONN_01X03; CONN_HEADER_2.54MM_1x3
J2: CORTEX_DEBUG_ETM; CONN_HEADER_1.27MM_2x10_SMT_SAMTEC_FTSH-110-01-L-DV-K
JP1, JP2, JP3, JP4: Jumper; CONN_HEADER_2.54MM_1x2
L1, L2, L3, L5, L6, L7: 2.2 uH; EIA_1210_CAP_NOSILK
R1: DNP; EIA_0402_RES_NOSILK
R2, R3: 33K; EIA_0402_RES_NOSILK
R4, R36, R40: 4.7K; EIA_0402_RES_NOSILK
R5, R13, R14, R15, R18, R19, R20, R77, R78, R79, R83, R84, R85, R88, R89, R90, R92: 10K; EIA_0402_RES_NOSILK
R6: 1K; EIA_0402_RES_NOSILK
R7: 33; EIA_0402_RES_NOSILK
R9, R21, R22, R23, R76, R80, R91, R93: 25 mR; EIA_0402_RES_NOSILK
R10: 0; EIA_0402_RES_NOSILK
R11, R16, R24: 280K; EIA_0402_RES_NOSILK
R12, R25: 88.7K; EIA_0402_RES_NOSILK
R17: 130K; EIA_0402_RES_NOSILK
R46, R81: 232K; EIA_0402_RES_NOSILK
R75: 187K; EIA_0402_RES_NOSILK
R82: 464K; EIA_0402_RES_NOSILK
R86: 255K; EIA_0402_RES_NOSILK
R87: 1.02M; EIA_0402_RES_NOSILK
SW1, SW2: SWITCH; SWITCH_RAFI_MICON_5
TP1, TP2, TP3, TP4, TP12, TP13, TP14, TP16: U.FL; CONN_U.FL_TE_1909763-1
TP15: CONN_01X08; CONN_HEADER_2.54MM_1x8
U2: STM32L431-QFN48; QFN_48_0.5MM_7x7MM
U3, U4, U5, U6, U7, U8, U9, U19: INA230; QFN_16_0.5MM_3x3MM
U10: NCP45525IMNTWG-H; DFN_8_0.5MM_2x2MM
U11: LTC3374-QFN; QFN_38_0.5MM_5x7MM

Connections:
/1V0: R86.1, R88.1, R91.1, TP14.1 (In), U19.11 (Vbus), U19.12 (Vin-); also elsewhere on the board
/1V2: JP4.1, R80.1, R81.1, R83.1, TP13.1 (In), U8.11 (Vbus), U8.12 (Vin-); also elsewhere on the board
/1V8: JP3.1, R46.1, R76.1, R77.1, TP12.1 (In), U7.11 (Vbus), U7.12 (Vin-); also elsewhere on the board
/2V5: JP2.1, R16.1, R18.1, R22.1, TP3.1 (In), U6.11 (Vbus), U6.12 (Vin-); also elsewhere on the board
/3V3: C176.1, JP1.1, R11.1, R13.1, R21.1, TP1.1 (In), U5.11 (Vbus), U5.12 (Vin-), U10.3 (VCC); also elsewhere on the board
/3V3_SB: C1.1, C2.1, C4.1, C6.1, C7.1, C8.1, C9.1, C10.1, C11.1, C12.1, C13.1, C14.1, C15.1, C175.1, FB1.2, J2.1 (VCC), R1.1, R6.1, R23.1, R24.1, R36.1, R40.1, SW1.2, SW2.2, TP4.1 (In), U2.1 (VBAT), U2.24 (VDD), U2.36 (VDD), U2.48 (VDD), U3.9 (Vs+), U4.2 (A0), U4.9 (Vs+), U4.11 (Vbus), U4.12 (Vin-), U5.9 (Vs+), U6.9 (Vs+), U7.1 (A1), U7.9 (Vs+), U8.1 (A1), U8.2 (A0), U8.9 (Vs+), U9.1 (A1), U9.9 (Vs+), U19.1 (A1), U19.9 (Vs+); also elsewhere on the board
/DUT_VCCIO_EN: TP15.4, U2.33 (PA12); also elsewhere on the board
/DUT_VDD: R93.1, TP16.1 (In), U9.11 (Vbus), U9.12 (Vin-); also elsewhere on the board
/FPGA support/FPGA_INIT: U2.28 (PB15); also elsewhere on the board
/FPGA support/FPGA_RST_N: U2.29 (PA8); also elsewhere on the board
/FPGA_DONE: U2.32 (PA11); also elsewhere on the board
/GND: C1.2, C2.2, C3.2, C4.2, C5.2, C6.2, C7.2, C8.2, C9.2, C10.2, C11.2, C12.2, C13.2, C14.2, C15.2, C16.2, C91.2, C92.2, C93.2, C94.2, C95.2, C96.2, C97.2, C98.2, C99.2, C100.2, C101.2, C135.2, C166.2, C167.2, C168.2, C169.2, C170.2, C171.2, C172.2, C173.2, C174.2, C175.2, C176.2, C177.2, D1.1 (K), D2.1 (K), D3.1 (K), J1.3, J2.3 (GND), J2.5 (GND), J2.9 (GNDdet), J2.11 (GND), J2.13 (GND), J2.15 (GND), J2.17 (GND), J2.19 (GND), R5.2, R10.2, R12.2, R14.2, R15.2, R17.2, R19.2, R20.2, R25.2, R75.2, R78.2, R79.2, R82.2, R84.2, R85.2, R87.2, R89.2, R90.2, R92.2, TP1.2 (Ext), TP2.2 (Ext), TP3.2 (Ext), TP4.2 (Ext), TP12.2 (Ext), TP13.2 (Ext), TP14.2 (Ext), TP15.1, TP15.8, TP16.2 (Ext), U2.8 (VSSA), U2.23 (GND), U2.35 (GND), U2.47 (GND), U2.PAD (GND), U3.1 (A1), U3.2 (A0), U3.10 (GND), U3.PAD (GND), U4.1 (A1), U4.10 (GND), U4.PAD (GND), U5.1 (A1), U5.10 (GND), U5.PAD (GND), U6.1 (A1), U6.10 (GND), U6.PAD (GND), U7.2 (A0), U7.10 (GND), U7.PAD (GND), U8.10 (GND), U8.PAD (GND), U9.10 (GND), U9.PAD (GND), U10.4 (GND), U11.16 (SYNC), U11.32 (EN8), U11.37 (EN2), U11.PAD (GND), U19.10 (GND), U19.PAD (GND); also elsewhere on the board
/INA_ALERT: TP15.5, U2.41 (PB5), U3.3 (Alert), U4.3 (Alert), U5.3 (Alert), U6.3 (Alert), U7.3 (Alert), U8.3 (Alert), U9.3 (Alert), U19.3 (Alert); also elsewhere on the board
/MCU/MCU_RST_N: U2.25 (PB12); also elsewhere on the board
/MCU/SUPER_SPI_CS_N: U2.14 (SPI1_NSS); also elsewhere on the board
/MCU/SUPER_SPI_MISO: U2.16 (SPI1_MISO); also elsewhere on the board
/MCU/SUPER_SPI_MOSI: U2.17 (SPI1_MOSI); also elsewhere on the board
/MCU/SUPER_SPI_SCK: U2.15 (SPI1_SCK); also elsewhere on the board
/Power supply/1V0_DIV2: R88.2, R89.1, U2.19 (ADC1_IN16)
/Power supply/1V0_EN: R90.1, U2.6 (PH1), U11.33 (EN7)
/Power supply/1V0_FB: R86.2, R87.1, U11.26 (FB7)
/Power supply/1V0_SHIN: C174.1, L7.1, R91.2, U19.13 (Vin+)
/Power supply/1V0_SW: L7.2, U11.28 (SW7), U11.29 (SW8)
/Power supply/1V2_DIV2: R83.2, R84.1, U2.13 (ADC1_IN8)
/Power supply/1V2_EN: R85.1, U2.21 (PB10), U11.18 (EN6)
/Power supply/1V2_FB: R81.2, R82.1, U11.25 (FB6)
/Power supply/1V2_SHIN: C168.1, L6.1, R80.2, U8.13 (Vin+)
/Power supply/1V8_DIV2: R77.2, R78.1, U2.18 (ADC1_IN15)
/Power supply/1V8_EN: R79.1, U2.20 (PB2), U11.19 (EN5)
/Power supply/1V8_FB: R46.2, R75.1, U11.20 (FB5)
/Power supply/1V8_SHIN: C135.1, L5.1, R76.2, U7.13 (Vin+)
/Power supply/2V5_DIV2: R18.2, R19.1, U2.12 (ADC1_IN7)
/Power supply/2V5_EN: R20.1, U2.2 (PC13), U11.14 (EN3)
/Power supply/2V5_FB: R16.2, R17.1, U11.7 (FB3)
/Power supply/2V5_SHIN: C95.1, L2.1, R22.2, U6.13 (Vin+)
/Power supply/3V3_DIV2: R13.2, R14.1, U2.11 (ADC1_IN6)
/Power supply/3V3_EN: R15.1, U2.4 (PC15), U11.38 (EN1)
/Power supply/3V3_FB: R11.2, R12.1, U11.1 (FB1)
/Power supply/3V3_SB_FB: R24.2, R25.1, U11.12 (FB4)
/Power supply/3V3_SB_SHIN: C99.1, L3.1, R23.2, U4.13 (Vin+)
/Power supply/3V3_SHIN: C92.1, L1.1, R21.2, U5.13 (Vin+)
/Power supply/3V3_SW: L1.2, U11.3 (SW1), U11.4 (SW2)
/Power supply/A3V3_SUPER: C5.1, FB1.1, U2.9 (VDDA)
/Power supply/DUT_VDD_EN: R92.1, TP15.3, U2.3 (PC14), U10.2 (EN)
/Power supply/DUT_VDD_RAW: JP1.2, JP2.2, JP3.2, JP4.2, U10.1 (VIN), U10.PAD (VIN)
/Power supply/DUT_VDD_SHIN: C16.1, R93.2, U9.13 (Vin+), U10.5 (BLEED), U10.7 (VOUT), U10.8 (VOUT)
/Power supply/LTC_PGOOD_ALL: TP15.2, U2.22 (PB11), U11.15 (PGOOD_ALL)
/Power supply/LTC_VTEMP: U2.10 (ADC1_IN5), U11.36 (TEMP)
/Power supply/SOFT_PWR: SW1.1, U2.26 (PB13)
/Power supply/SOFT_RST: SW2.1, U2.27 (PB14)
/Power supply/SUPER_BOOT0: R5.1, U2.44 (BOOT0)
/Power supply/SUPER_FAULT_LED: R4.1, U2.45 (PB8)
/Power supply/SUPER_JTAG_TCK: J2.4 (TCK), U2.37 (JTCK)
/Power supply/SUPER_JTAG_TDI: J2.8 (TDI), U2.38 (JTDI)
/Power supply/SUPER_JTAG_TDO: J2.6 (TDO), R7.1
/Power supply/SUPER_JTAG_TMS: J2.2 (TMS), U2.34 (JTMS)
/Power supply/SUPER_JTAG_TRST: R6.2, U2.40 (NJTRST)
/Power supply/SUPER_PWRGOOD_LED: R2.1, U2.46 (PB9)
/Power supply/SUPER_RST_N: C3.1, J2.10 (~RST), R1.2, U2.7 (NRST)
/Power supply/SUPER_SYSOK_LED: R3.1, U2.5 (PH0)
/Power supply/SUPER_UART_RX: J1.1, U2.31 (USART1_RX)
/Power supply/SUPER_UART_TX: J1.2, U2.30 (USART1_TX)
/SUPER_I2C_SCL: R36.2, TP15.7, U2.42 (I2C1_SCL), U3.5 (SCL), U4.5 (SCL), U5.5 (SCL), U6.2 (A0), U6.5 (SCL), U7.5 (SCL), U8.5 (SCL), U9.2 (A0), U9.5 (SCL), U19.5 (SCL); also elsewhere on the board
/SUPER_I2C_SDA: R40.2, TP15.6, U2.43 (I2C1_SDA), U3.4 (SDA), U4.4 (SDA), U5.2 (A0), U5.4 (SDA), U6.4 (SDA), U7.4 (SDA), U8.4 (SDA), U9.4 (SDA), U19.2 (A0), U19.4 (SDA); also elsewhere on the board
/VBUS: R9.2, U3.13 (Vin+); also elsewhere on the board
/VBUS_SHOUT: C91.1, C93.1, C94.1, C96.1, C97.1, C98.1, C100.1, C101.1, C166.1, C167.1, C169.1, C170.1, C171.1, C172.1, C173.1, R9.1, TP2.1 (In), U3.11 (Vbus), U3.12 (Vin-), U11.2 (VIN1), U11.5 (VIN2), U11.6 (FB2), U11.8 (VIN3), U11.11 (VIN4), U11.13 (EN4), U11.17 (RT), U11.21 (VIN5), U11.24 (VIN6), U11.27 (VIN7), U11.30 (VIN8), U11.31 (FB8), U11.35 (VCC); also elsewhere on the board
unnamed: D1.2 (A), R2.2
unnamed: D2.2 (A), R3.2
unnamed: D3.2 (A), R4.2
unnamed: R7.2, U2.39 (JTDO)
unnamed: C177.1, U10.6 (SR)
unnamed: L2.2, U11.9 (SW3)
unnamed: L3.2, U11.10 (SW4)
unnamed: L5.2, U11.22 (SW5)
unnamed: L6.2, U11.23 (SW6)
unnamed: R10.1, U11.34 (MODE)

Notes on the sheet:
3V3 current monitor: 0x84
VBUS current monitor: 0x80
3V3_SB current monitor: 0x82
DUT_VDD current monitor: 0x8e
2V5 current monitor: 0x86
1V0 current monitor: 0x8c
1V2 current monitor: 0x8a
1V8 current monitor: 0x88
Use divided rails as ADC inputs for sequencing decisions and system safety checks only Use INA230 (slower but more accurate) for anything not time critical
Aim for 25 mV drop on shunts at 1A load? That's 25 milliohms
