azonenberg/dumptruck/main-pcb/main-pcb.kicad_pcb

## KiCad design main-pcb/main-pcb.kicad_pcb (continued)

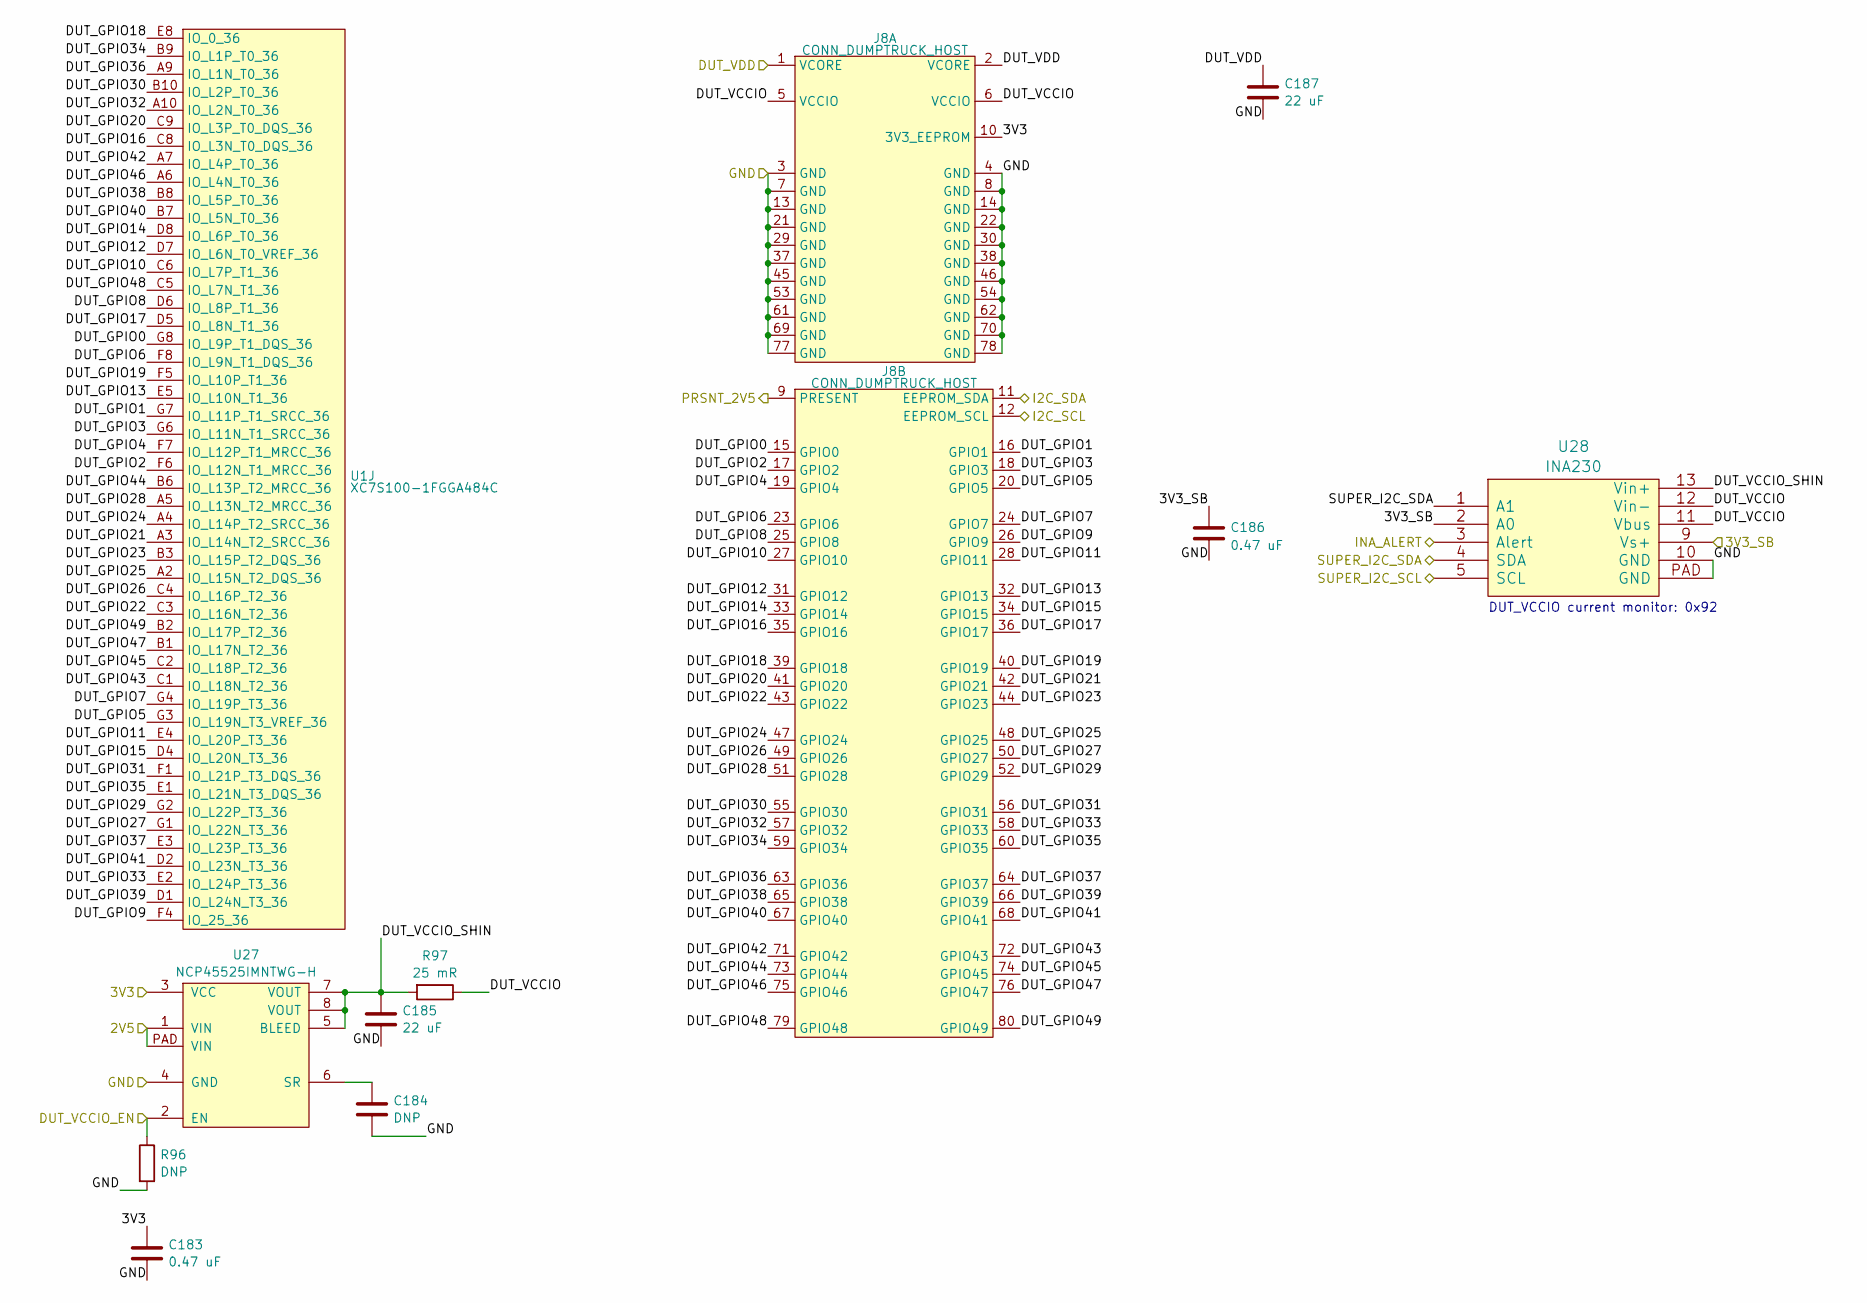
[picture p37: schematic 2v5_vccio.kicad_sch, DUMPTRUCK flash dumper]

Parts:
C183, C186: 0.47 uF; EIA_0402_CAP_NOSILK
C184: DNP; EIA_0402_CAP_NOSILK
C185, C187: 22 uF; EIA_1206_CAP_NOSILK
J8: CONN_DUMPTRUCK_HOST; CONN_SAMTEC_BTE-040-01-F-D-A-K
R96: DNP; EIA_0402_RES_NOSILK
R97: 25 mR; EIA_0402_RES_NOSILK
U1: XC7S100-1FGGA484C; BGA_484_22x22_FULLARRAY_1MM
U27: NCP45525IMNTWG-H; DFN_8_0.5MM_2x2MM
U28: INA230; QFN_16_0.5MM_3x3MM

Connections:
/2V5: U27.1 (VIN), U27.PAD (VIN); also elsewhere on the board
/2V5 VCCIO socket/DUT_GPIO0: J8.15 (GPIO0), U1.G8 (IO_L9P_T1_DQS_36)
/2V5 VCCIO socket/DUT_GPIO1: J8.16 (GPIO1), U1.G7 (IO_L11P_T1_SRCC_36)
/2V5 VCCIO socket/DUT_GPIO2: J8.17 (GPIO2), U1.F6 (IO_L12N_T1_MRCC_36)
/2V5 VCCIO socket/DUT_GPIO3: J8.18 (GPIO3), U1.G6 (IO_L11N_T1_SRCC_36)
/2V5 VCCIO socket/DUT_GPIO4: J8.19 (GPIO4), U1.F7 (IO_L12P_T1_MRCC_36)
/2V5 VCCIO socket/DUT_GPIO5: J8.20 (GPIO5), U1.G3 (IO_L19N_T3_VREF_36)
/2V5 VCCIO socket/DUT_GPIO6: J8.23 (GPIO6), U1.F8 (IO_L9N_T1_DQS_36)
/2V5 VCCIO socket/DUT_GPIO7: J8.24 (GPIO7), U1.G4 (IO_L19P_T3_36)
/2V5 VCCIO socket/DUT_GPIO8: J8.25 (GPIO8), U1.D6 (IO_L8P_T1_36)
/2V5 VCCIO socket/DUT_GPIO9: J8.26 (GPIO9), U1.F4 (IO_25_36)
/2V5 VCCIO socket/DUT_GPIO10: J8.27 (GPIO10), U1.C6 (IO_L7P_T1_36)
/2V5 VCCIO socket/DUT_GPIO11: J8.28 (GPIO11), U1.E4 (IO_L20P_T3_36)
/2V5 VCCIO socket/DUT_GPIO12: J8.31 (GPIO12), U1.D7 (IO_L6N_T0_VREF_36)
/2V5 VCCIO socket/DUT_GPIO13: J8.32 (GPIO13), U1.E5 (IO_L10N_T1_36)
/2V5 VCCIO socket/DUT_GPIO14: J8.33 (GPIO14), U1.D8 (IO_L6P_T0_36)
/2V5 VCCIO socket/DUT_GPIO15: J8.34 (GPIO15), U1.D4 (IO_L20N_T3_36)
/2V5 VCCIO socket/DUT_GPIO16: J8.35 (GPIO16), U1.C8 (IO_L3N_T0_DQS_36)
/2V5 VCCIO socket/DUT_GPIO17: J8.36 (GPIO17), U1.D5 (IO_L8N_T1_36)
/2V5 VCCIO socket/DUT_GPIO18: J8.39 (GPIO18), U1.E8 (IO_0_36)
/2V5 VCCIO socket/DUT_GPIO19: J8.40 (GPIO19), U1.F5 (IO_L10P_T1_36)
/2V5 VCCIO socket/DUT_GPIO20: J8.41 (GPIO20), U1.C9 (IO_L3P_T0_DQS_36)
/2V5 VCCIO socket/DUT_GPIO21: J8.42 (GPIO21), U1.A3 (IO_L14N_T2_SRCC_36)
/2V5 VCCIO socket/DUT_GPIO22: J8.43 (GPIO22), U1.C3 (IO_L16N_T2_36)
/2V5 VCCIO socket/DUT_GPIO23: J8.44 (GPIO23), U1.B3 (IO_L15P_T2_DQS_36)
/2V5 VCCIO socket/DUT_GPIO24: J8.47 (GPIO24), U1.A4 (IO_L14P_T2_SRCC_36)
/2V5 VCCIO socket/DUT_GPIO25: J8.48 (GPIO25), U1.A2 (IO_L15N_T2_DQS_36)
/2V5 VCCIO socket/DUT_GPIO26: J8.49 (GPIO26), U1.C4 (IO_L16P_T2_36)
/2V5 VCCIO socket/DUT_GPIO27: J8.50 (GPIO27), U1.G1 (IO_L22N_T3_36)
/2V5 VCCIO socket/DUT_GPIO28: J8.51 (GPIO28), U1.A5 (IO_L13N_T2_MRCC_36)
/2V5 VCCIO socket/DUT_GPIO29: J8.52 (GPIO29), U1.G2 (IO_L22P_T3_36)
/2V5 VCCIO socket/DUT_GPIO30: J8.55 (GPIO30), U1.B10 (IO_L2P_T0_36)
/2V5 VCCIO socket/DUT_GPIO31: J8.56 (GPIO31), U1.F1 (IO_L21P_T3_DQS_36)
/2V5 VCCIO socket/DUT_GPIO32: J8.57 (GPIO32), U1.A10 (IO_L2N_T0_36)
/2V5 VCCIO socket/DUT_GPIO33: J8.58 (GPIO33), U1.E2 (IO_L24P_T3_36)
/2V5 VCCIO socket/DUT_GPIO34: J8.59 (GPIO34), U1.B9 (IO_L1P_T0_36)
/2V5 VCCIO socket/DUT_GPIO35: J8.60 (GPIO35), U1.E1 (IO_L21N_T3_DQS_36)
/2V5 VCCIO socket/DUT_GPIO36: J8.63 (GPIO36), U1.A9 (IO_L1N_T0_36)
/2V5 VCCIO socket/DUT_GPIO37: J8.64 (GPIO37), U1.E3 (IO_L23P_T3_36)
/2V5 VCCIO socket/DUT_GPIO38: J8.65 (GPIO38), U1.B8 (IO_L5P_T0_36)
/2V5 VCCIO socket/DUT_GPIO39: J8.66 (GPIO39), U1.D1 (IO_L24N_T3_36)
/2V5 VCCIO socket/DUT_GPIO40: J8.67 (GPIO40), U1.B7 (IO_L5N_T0_36)
/2V5 VCCIO socket/DUT_GPIO41: J8.68 (GPIO41), U1.D2 (IO_L23N_T3_36)
/2V5 VCCIO socket/DUT_GPIO42: J8.71 (GPIO42), U1.A7 (IO_L4P_T0_36)
/2V5 VCCIO socket/DUT_GPIO43: J8.72 (GPIO43), U1.C1 (IO_L18N_T2_36)
/2V5 VCCIO socket/DUT_GPIO44: J8.73 (GPIO44), U1.B6 (IO_L13P_T2_MRCC_36)
/2V5 VCCIO socket/DUT_GPIO45: J8.74 (GPIO45), U1.C2 (IO_L18P_T2_36)
/2V5 VCCIO socket/DUT_GPIO46: J8.75 (GPIO46), U1.A6 (IO_L4N_T0_36)
/2V5 VCCIO socket/DUT_GPIO47: J8.76 (GPIO47), U1.B1 (IO_L17N_T2_36)
/2V5 VCCIO socket/DUT_GPIO48: J8.79 (GPIO48), U1.C5 (IO_L7N_T1_36)
/2V5 VCCIO socket/DUT_GPIO49: J8.80 (GPIO49), U1.B2 (IO_L17P_T2_36)
/2V5 VCCIO socket/DUT_VCCIO: J8.5 (VCCIO), J8.6 (VCCIO), R97.1, U28.11 (Vbus), U28.12 (Vin-)
/2V5 VCCIO socket/DUT_VCCIO_SHIN: C185.1, R97.2, U27.5 (BLEED), U27.7 (VOUT), U27.8 (VOUT), U28.13 (Vin+)
/3V3: C183.1, J8.10 (3V3_EEPROM), U27.3 (VCC); also elsewhere on the board
/3V3_SB: C186.1, U28.2 (A0), U28.9 (Vs+); also elsewhere on the board
/DUT_VCCIO_EN: R96.1, U27.2 (EN); also elsewhere on the board
/DUT_VDD: C187.1, J8.1 (VCORE), J8.2 (VCORE); also elsewhere on the board
/GND: C183.2, C184.2, C185.2, C186.2, C187.2, J8.3 (GND), J8.4 (GND), J8.7 (GND), J8.8 (GND), J8.13 (GND), J8.14 (GND), J8.21 (GND), J8.22 (GND), J8.29 (GND), J8.30 (GND), J8.37 (GND), J8.38 (GND), J8.45 (GND), J8.46 (GND), J8.53 (GND), J8.54 (GND), J8.61 (GND), J8.62 (GND), J8.69 (GND), J8.70 (GND), J8.77 (GND), J8.78 (GND), R96.2, U27.4 (GND), U28.10 (GND), U28.PAD (GND); also elsewhere on the board
/I2C_SCL: J8.12 (EEPROM_SCL); also elsewhere on the board
/I2C_SDA: J8.11 (EEPROM_SDA); also elsewhere on the board
/INA_ALERT: U28.3 (Alert); also elsewhere on the board
/PRSNT_2V5: J8.9 (PRESENT); also elsewhere on the board
/SUPER_I2C_SCL: U28.5 (SCL); also elsewhere on the board
/SUPER_I2C_SDA: U28.1 (A1), U28.4 (SDA); also elsewhere on the board
unnamed: C184.1, U27.6 (SR)

Notes on the sheet:
DUT_VCCIO current monitor: 0x92

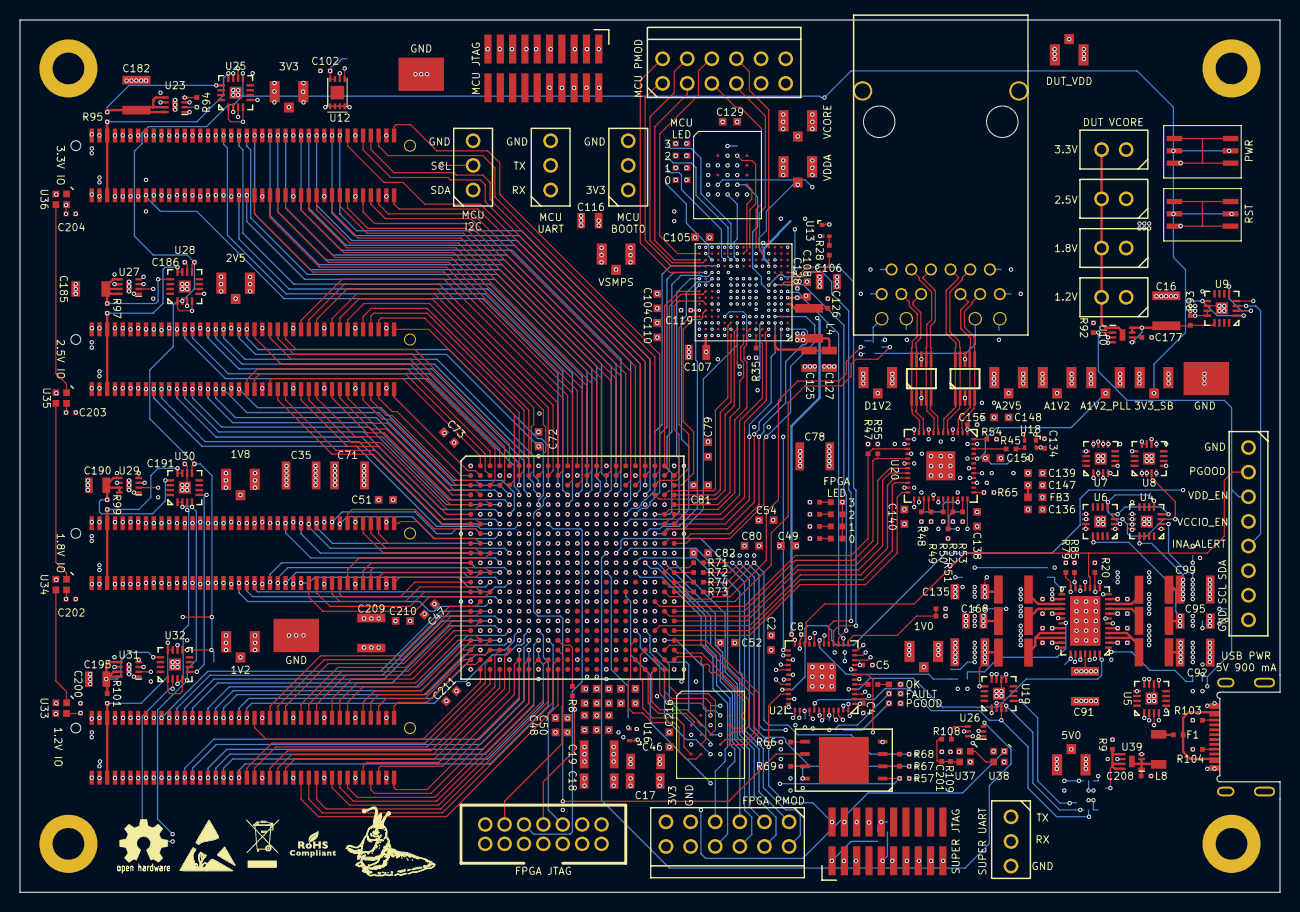
[picture p38: board main-pcb.kicad_pcb from above]

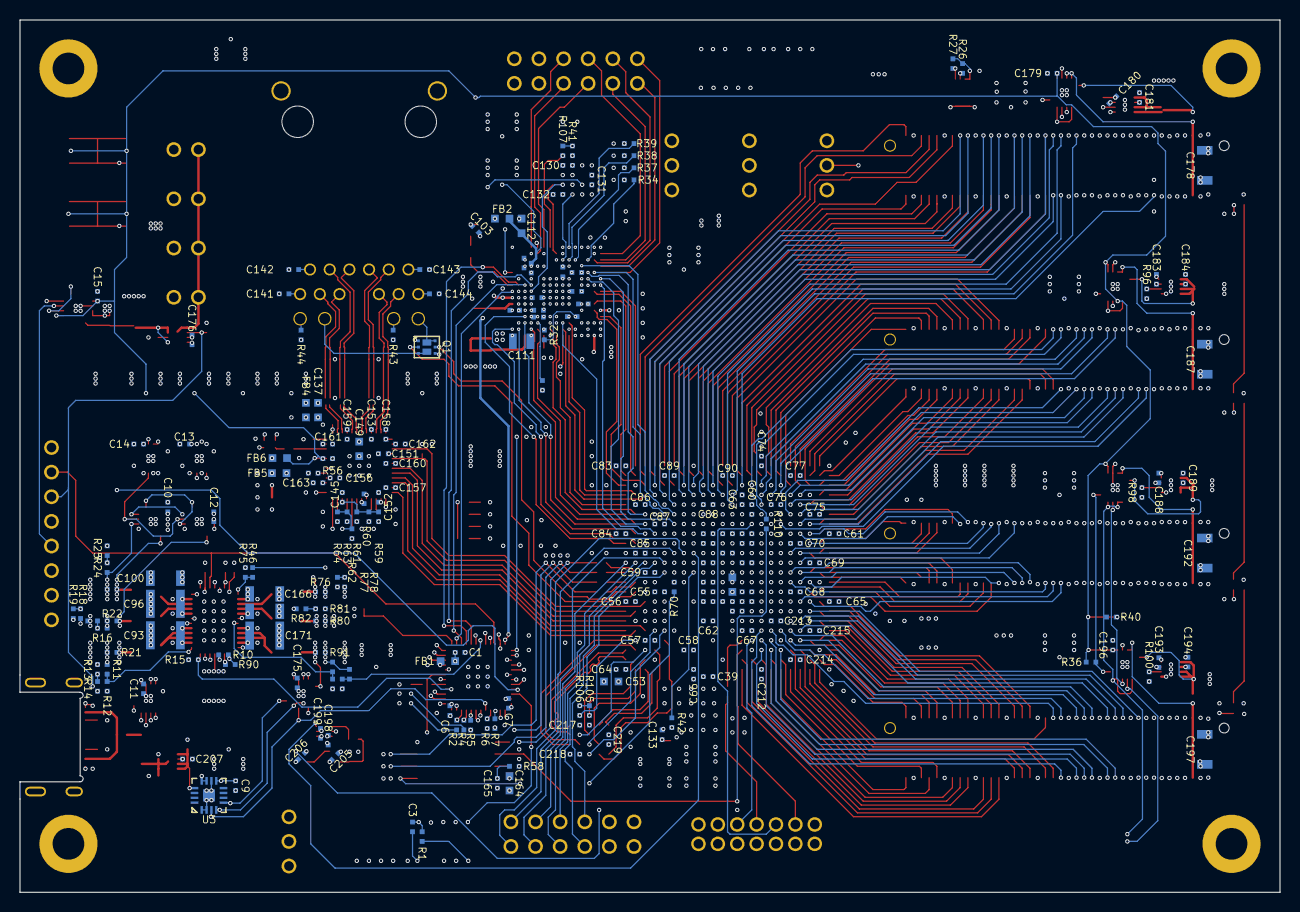
[picture p39: board main-pcb.kicad_pcb from below]

Board: 10 copper layers, 130.0 x 90.0 mm, 444 parts (203 on the bottom side), 492 nets.
